yilmaz-kaan/OpenPhasedArray/Software/TXBoardData2/amp_imbalance.png

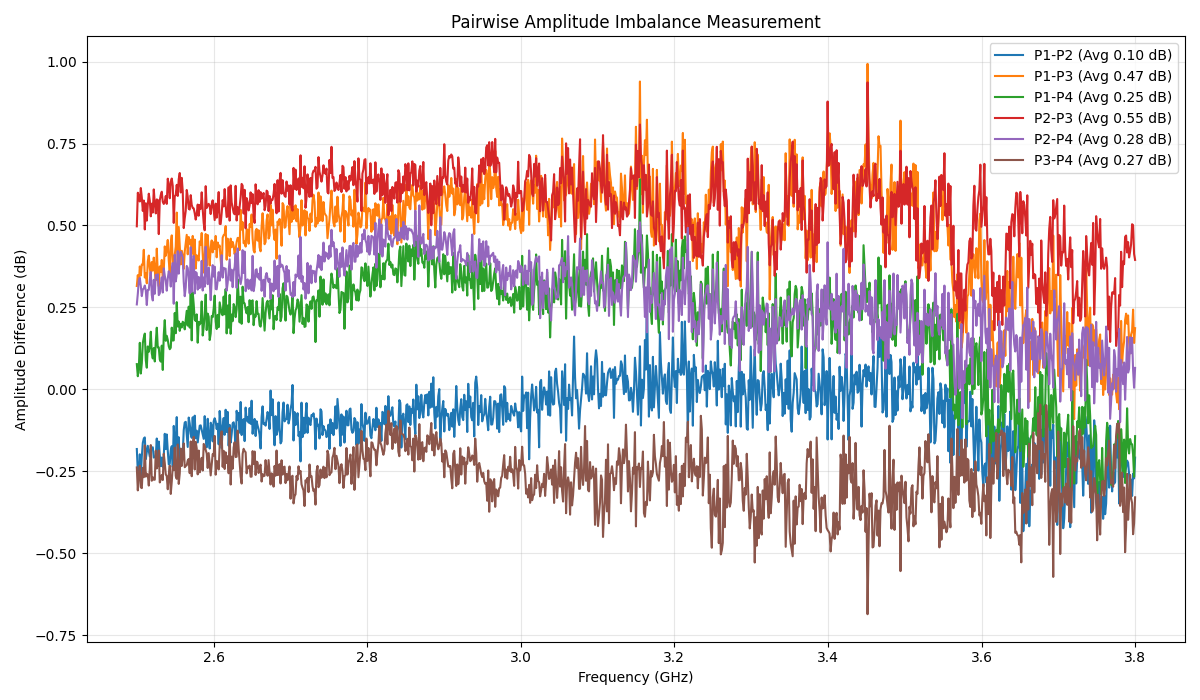
Software/TXBoardData2/amp_imbalance.png
