yilmaz-kaan/OpenPhasedArray/Software/TXBoardData2/phase_imbalance.png

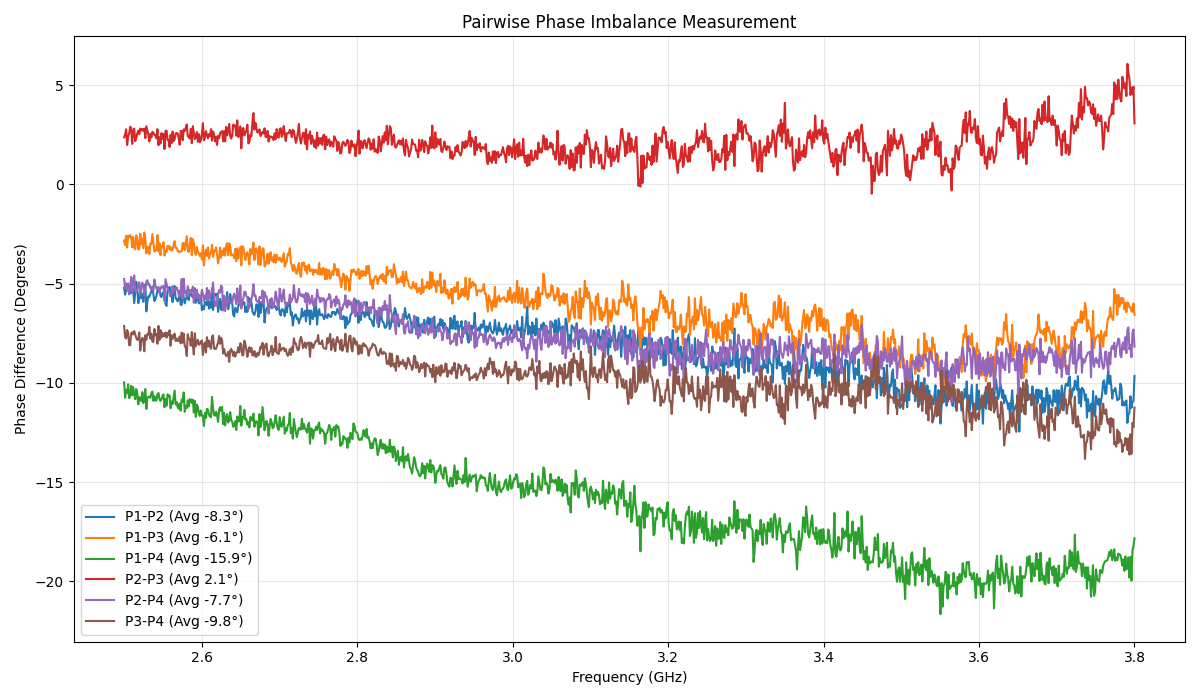
Software/TXBoardData2/phase_imbalance.png
