yilmaz-kaan/OpenPhasedArray/Software/TXBoardData2/s21_magnitude_plot.png

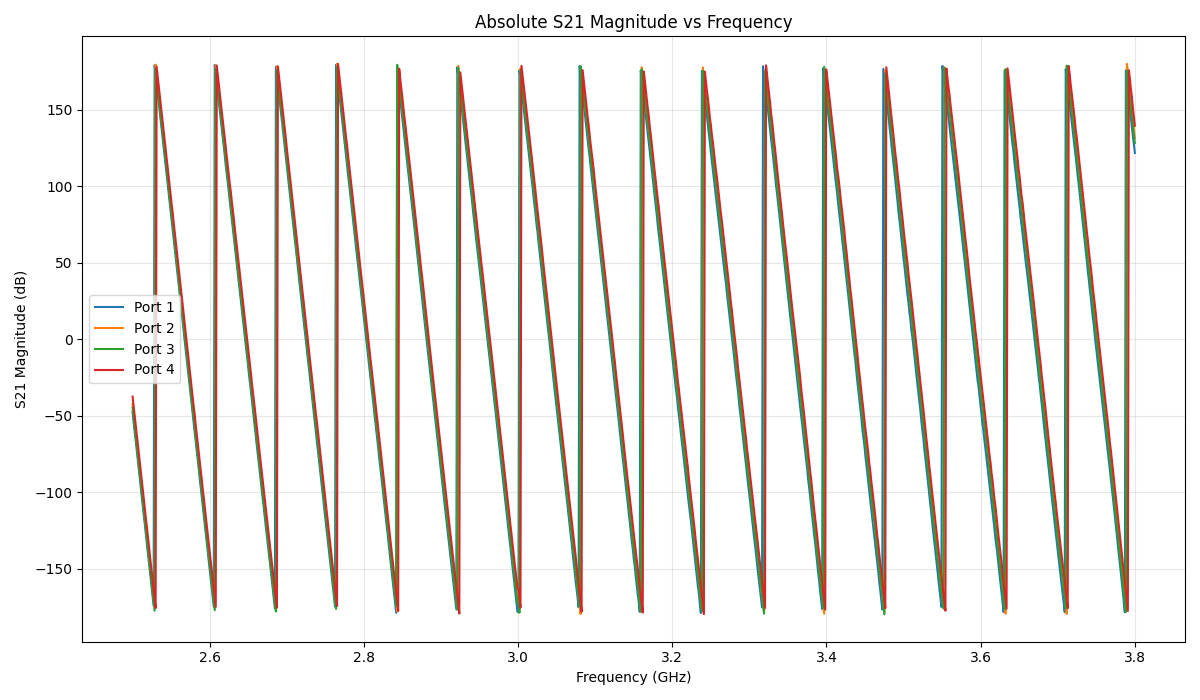
Software/TXBoardData2/s21_magnitude_plot.png
