yilmaz-kaan/OpenPhasedArray/Software/ChamberTesting/sweep_results/ang_+000/phase_sweep_20260409_190627.csv

timestamp | n | m | ph1 | ph2 | ph3 | ph4 | power_dbm | freq_hz
2026-04-09T19:06:29.300982 | 0 | 0 | 0 | 0 | 0 | 0 | -71.4100 | 2399999999.90
2026-04-09T19:06:31.392526 | 0 | 1 | 0 | 1 | 2 | 3 | -72.4100 | 2399999999.90
2026-04-09T19:06:33.485229 | 0 | 2 | 0 | 2 | 4 | 6 | -72.1000 | 2399999999.80
2026-04-09T19:06:35.580663 | 0 | 3 | 0 | 3 | 6 | 9 | -71.8600 | 2399999999.90
2026-04-09T19:06:37.671744 | 0 | 4 | 0 | 4 | 8 | 12 | -71.1500 | 2399999999.69
2026-04-09T19:06:39.762542 | 0 | 5 | 0 | 5 | 10 | 15 | -70.4400 | 2399999999.90
2026-04-09T19:06:41.852031 | 0 | 6 | 0 | 6 | 12 | 18 | -69.8200 | 2399999999.90
2026-04-09T19:06:43.941766 | 0 | 7 | 0 | 7 | 14 | 21 | -69.1300 | 2399999999.90
2026-04-09T19:06:46.022581 | 0 | 8 | 0 | 8 | 16 | 24 | -68.7100 | 2399999999.90
2026-04-09T19:06:48.113687 | 0 | 9 | 0 | 9 | 18 | 27 | -68.4400 | 2399999999.90
2026-04-09T19:06:50.193851 | 0 | 10 | 0 | 10 | 20 | 30 | -68.3600 | 2399999999.90
2026-04-09T19:06:52.286126 | 0 | 11 | 0 | 11 | 22 | 33 | -68.3400 | 2400000000.00
2026-04-09T19:06:54.379145 | 0 | 12 | 0 | 12 | 24 | 36 | -68.5800 | 2399999999.90
2026-04-09T19:06:56.465394 | 0 | 13 | 0 | 13 | 26 | 39 | -68.9800 | 2400000000.00
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
