yilmaz-kaan/OpenPhasedArray/Software/ChamberTesting/sweep_results/ang_+010/phase_sweep_20260409_192429.csv

timestamp | n | m | ph1 | ph2 | ph3 | ph4 | power_dbm | freq_hz
2026-04-09T19:24:32.037245 | 0 | 0 | 0 | 0 | 0 | 0 | -70.7900 | 2399999999.90
2026-04-09T19:24:34.134366 | 0 | 1 | 0 | 1 | 2 | 3 | -70.7300 | 2400000000.00
2026-04-09T19:24:36.229806 | 0 | 2 | 0 | 2 | 4 | 6 | -70.2400 | 2399999999.80
2026-04-09T19:24:38.324632 | 0 | 3 | 0 | 3 | 6 | 9 | -69.7700 | 2399999999.90
2026-04-09T19:24:40.418706 | 0 | 4 | 0 | 4 | 8 | 12 | -69.6800 | 2400000000.00
2026-04-09T19:24:42.508899 | 0 | 5 | 0 | 5 | 10 | 15 | -69.3500 | 2400000000.00
2026-04-09T19:24:44.606124 | 0 | 6 | 0 | 6 | 12 | 18 | -69.2600 | 2399999999.90
2026-04-09T19:24:46.698053 | 0 | 7 | 0 | 7 | 14 | 21 | -69.0800 | 2400000000.00
2026-04-09T19:24:48.781957 | 0 | 8 | 0 | 8 | 16 | 24 | -69.2700 | 2400000000.00
2026-04-09T19:24:50.884232 | 0 | 9 | 0 | 9 | 18 | 27 | -69.4100 | 2399999999.90
2026-04-09T19:24:52.974033 | 0 | 10 | 0 | 10 | 20 | 30 | -69.7900 | 2399999999.80
2026-04-09T19:24:55.054822 | 0 | 11 | 0 | 11 | 22 | 33 | -69.9200 | 2399999999.90
2026-04-09T19:24:57.141785 | 0 | 12 | 0 | 12 | 24 | 36 | -70.3000 | 2400000000.00
2026-04-09T19:24:59.232864 | 0 | 13 | 0 | 13 | 26 | 39 | -70.1900 | 2399999999.90
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
