yilmaz-kaan/OpenPhasedArray/Software/ChamberTesting/sweep_results/ang_+015/phase_sweep_20260409_193331.csv

timestamp | n | m | ph1 | ph2 | ph3 | ph4 | power_dbm | freq_hz
2026-04-09T19:33:33.427099 | 0 | 0 | 0 | 0 | 0 | 0 | -71.9300 | 2399999999.90
2026-04-09T19:33:35.512890 | 0 | 1 | 0 | 1 | 2 | 3 | -70.1900 | 2399999999.80
2026-04-09T19:33:37.604410 | 0 | 2 | 0 | 2 | 4 | 6 | -69.3100 | 2399999999.90
2026-04-09T19:33:39.693443 | 0 | 3 | 0 | 3 | 6 | 9 | -68.3500 | 2400000000.00
2026-04-09T19:33:41.779738 | 0 | 4 | 0 | 4 | 8 | 12 | -68.2300 | 2399999999.90
2026-04-09T19:33:43.872867 | 0 | 5 | 0 | 5 | 10 | 15 | -67.8000 | 2400000000.00
2026-04-09T19:33:45.961199 | 0 | 6 | 0 | 6 | 12 | 18 | -67.7100 | 2400000000.00
2026-04-09T19:33:48.042742 | 0 | 7 | 0 | 7 | 14 | 21 | -67.5100 | 2399999999.80
2026-04-09T19:33:50.132148 | 0 | 8 | 0 | 8 | 16 | 24 | -67.6300 | 2399999999.90
2026-04-09T19:33:52.229259 | 0 | 9 | 0 | 9 | 18 | 27 | -67.6000 | 2399999999.90
2026-04-09T19:33:54.323774 | 0 | 10 | 0 | 10 | 20 | 30 | -67.6900 | 2399999999.90
2026-04-09T19:33:56.415985 | 0 | 11 | 0 | 11 | 22 | 33 | -67.5000 | 2399999999.90
2026-04-09T19:33:58.516901 | 0 | 12 | 0 | 12 | 24 | 36 | -67.5100 | 2400000000.00
2026-04-09T19:34:00.602896 | 0 | 13 | 0 | 13 | 26 | 39 | -67.1100 | 2399999999.90
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
