yilmaz-kaan/OpenPhasedArray/Software/ChamberTesting/sweep_results/ang_+020/phase_sweep_20260409_194232.csv

timestamp | n | m | ph1 | ph2 | ph3 | ph4 | power_dbm | freq_hz
2026-04-09T19:42:34.784234 | 0 | 0 | 0 | 0 | 0 | 0 | -66.1600 | 2400000000.00
2026-04-09T19:42:36.875792 | 0 | 1 | 0 | 1 | 2 | 3 | -65.5500 | 2399999999.90
2026-04-09T19:42:38.965969 | 0 | 2 | 0 | 2 | 4 | 6 | -65.2800 | 2399999999.90
2026-04-09T19:42:41.057895 | 0 | 3 | 0 | 3 | 6 | 9 | -64.9800 | 2399999999.90
2026-04-09T19:42:43.145978 | 0 | 4 | 0 | 4 | 8 | 12 | -64.9700 | 2399999999.90
2026-04-09T19:42:45.240022 | 0 | 5 | 0 | 5 | 10 | 15 | -64.8600 | 2399999999.90
2026-04-09T19:42:47.333413 | 0 | 6 | 0 | 6 | 12 | 18 | -64.8800 | 2399999999.90
2026-04-09T19:42:49.427156 | 0 | 7 | 0 | 7 | 14 | 21 | -64.8200 | 2400000000.00
2026-04-09T19:42:51.518538 | 0 | 8 | 0 | 8 | 16 | 24 | -64.8400 | 2399999999.90
2026-04-09T19:42:53.616594 | 0 | 9 | 0 | 9 | 18 | 27 | -64.8400 | 2399999999.90
2026-04-09T19:42:55.706537 | 0 | 10 | 0 | 10 | 20 | 30 | -64.7700 | 2399999999.80
2026-04-09T19:42:57.793736 | 0 | 11 | 0 | 11 | 22 | 33 | -64.6100 | 2399999999.90
2026-04-09T19:42:59.885695 | 0 | 12 | 0 | 12 | 24 | 36 | -64.4500 | 2400000000.00
2026-04-09T19:43:01.974687 | 0 | 13 | 0 | 13 | 26 | 39 | -64.2200 | 2399999999.80
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
