yilmaz-kaan/OpenPhasedArray/Software/ChamberTesting/sweep_results/ang_+025/phase_sweep_20260409_195133.csv

timestamp | n | m | ph1 | ph2 | ph3 | ph4 | power_dbm | freq_hz
2026-04-09T19:51:35.974541 | 0 | 0 | 0 | 0 | 0 | 0 | -65.1900 | 2399999999.90
2026-04-09T19:51:38.059181 | 0 | 1 | 0 | 1 | 2 | 3 | -64.7200 | 2400000000.00
2026-04-09T19:51:40.144102 | 0 | 2 | 0 | 2 | 4 | 6 | -64.4900 | 2399999999.90
2026-04-09T19:51:42.229900 | 0 | 3 | 0 | 3 | 6 | 9 | -64.2400 | 2399999999.90
2026-04-09T19:51:44.320964 | 0 | 4 | 0 | 4 | 8 | 12 | -64.0500 | 2399999999.90
2026-04-09T19:51:46.420974 | 0 | 5 | 0 | 5 | 10 | 15 | -63.8100 | 2400000000.00
2026-04-09T19:51:48.504114 | 0 | 6 | 0 | 6 | 12 | 18 | -63.6700 | 2400000000.00
2026-04-09T19:51:50.597637 | 0 | 7 | 0 | 7 | 14 | 21 | -63.4800 | 2399999999.90
2026-04-09T19:51:52.689689 | 0 | 8 | 0 | 8 | 16 | 24 | -63.2700 | 2399999999.90
2026-04-09T19:51:54.782009 | 0 | 9 | 0 | 9 | 18 | 27 | -63.1600 | 2399999999.90
2026-04-09T19:51:56.870397 | 0 | 10 | 0 | 10 | 20 | 30 | -62.9600 | 2399999999.90
2026-04-09T19:51:58.956115 | 0 | 11 | 0 | 11 | 22 | 33 | -62.8100 | 2399999999.90
2026-04-09T19:52:01.042364 | 0 | 12 | 0 | 12 | 24 | 36 | -62.5600 | 2399999999.90
2026-04-09T19:52:03.135037 | 0 | 13 | 0 | 13 | 26 | 39 | -62.4800 | 2400000000.00
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
