yilmaz-kaan/OpenPhasedArray/Software/ChamberTesting/sweep_results/ang_+030/phase_sweep_20260409_200035.csv

timestamp | n | m | ph1 | ph2 | ph3 | ph4 | power_dbm | freq_hz
2026-04-09T20:00:37.349513 | 0 | 0 | 0 | 0 | 0 | 0 | -67.6800 | 2399999999.90
2026-04-09T20:00:39.437083 | 0 | 1 | 0 | 1 | 2 | 3 | -67.1000 | 2399999999.90
2026-04-09T20:00:41.528277 | 0 | 2 | 0 | 2 | 4 | 6 | -66.8000 | 2399999999.90
2026-04-09T20:00:43.612792 | 0 | 3 | 0 | 3 | 6 | 9 | -66.3300 | 2399999999.90
2026-04-09T20:00:45.705344 | 0 | 4 | 0 | 4 | 8 | 12 | -65.9500 | 2399999999.80
2026-04-09T20:00:47.785598 | 0 | 5 | 0 | 5 | 10 | 15 | -65.4100 | 2399999999.90
2026-04-09T20:00:49.880581 | 0 | 6 | 0 | 6 | 12 | 18 | -65.0500 | 2400000000.00
2026-04-09T20:00:51.974999 | 0 | 7 | 0 | 7 | 14 | 21 | -64.6100 | 2399999999.80
2026-04-09T20:00:54.067591 | 0 | 8 | 0 | 8 | 16 | 24 | -64.1400 | 2400000000.00
2026-04-09T20:00:56.161253 | 0 | 9 | 0 | 9 | 18 | 27 | -63.8400 | 2399999999.90
2026-04-09T20:00:58.252232 | 0 | 10 | 0 | 10 | 20 | 30 | -63.4700 | 2399999999.90
2026-04-09T20:01:00.339875 | 0 | 11 | 0 | 11 | 22 | 33 | -63.2100 | 2399999999.90
2026-04-09T20:01:02.432898 | 0 | 12 | 0 | 12 | 24 | 36 | -62.8500 | 2400000000.00
2026-04-09T20:01:04.521017 | 0 | 13 | 0 | 13 | 26 | 39 | -62.7200 | 2400000000.00
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
