yilmaz-kaan/OpenPhasedArray/Software/ChamberTesting/sweep_results/ang_-005/phase_sweep_20260409_185726.csv

timestamp | n | m | ph1 | ph2 | ph3 | ph4 | power_dbm | freq_hz
2026-04-09T18:57:28.192007 | 0 | 0 | 0 | 0 | 0 | 0 | -66.4600 | 2399999999.90
2026-04-09T18:57:30.276454 | 0 | 1 | 0 | 1 | 2 | 3 | -67.8800 | 2399999999.90
2026-04-09T18:57:32.355722 | 0 | 2 | 0 | 2 | 4 | 6 | -68.6300 | 2399999999.80
2026-04-09T18:57:34.439189 | 0 | 3 | 0 | 3 | 6 | 9 | -70.4000 | 2399999999.90
2026-04-09T18:57:36.528013 | 0 | 4 | 0 | 4 | 8 | 12 | -70.7800 | 2399999999.90
2026-04-09T18:57:38.619984 | 0 | 5 | 0 | 5 | 10 | 15 | -72.0100 | 2399999999.90
2026-04-09T18:57:40.705919 | 0 | 6 | 0 | 6 | 12 | 18 | -71.9600 | 2399999999.90
2026-04-09T18:57:42.796384 | 0 | 7 | 0 | 7 | 14 | 21 | -71.5200 | 2399999999.90
2026-04-09T18:57:44.882963 | 0 | 8 | 0 | 8 | 16 | 24 | -70.5100 | 2400000000.00
2026-04-09T18:57:46.976137 | 0 | 9 | 0 | 9 | 18 | 27 | -69.6900 | 2400000000.00
2026-04-09T18:57:49.063926 | 0 | 10 | 0 | 10 | 20 | 30 | -68.9200 | 2399999999.90
2026-04-09T18:57:51.150750 | 0 | 11 | 0 | 11 | 22 | 33 | -68.2800 | 2399999999.90
2026-04-09T18:57:53.241819 | 0 | 12 | 0 | 12 | 24 | 36 | -67.9100 | 2399999999.90
2026-04-09T18:57:55.326955 | 0 | 13 | 0 | 13 | 26 | 39 | -67.6500 | 2399999999.90
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
