yilmaz-kaan/OpenPhasedArray/Software/ChamberTesting/sweep_results/ang_-010/phase_sweep_20260409_184824.csv

timestamp | n | m | ph1 | ph2 | ph3 | ph4 | power_dbm | freq_hz
2026-04-09T18:48:26.828237 | 0 | 0 | 0 | 0 | 0 | 0 | -62.3600 | 2400000000.00
2026-04-09T18:48:28.917014 | 0 | 1 | 0 | 1 | 2 | 3 | -63.0900 | 2399999999.90
2026-04-09T18:48:31.004669 | 0 | 2 | 0 | 2 | 4 | 6 | -63.4000 | 2399999999.90
2026-04-09T18:48:33.090127 | 0 | 3 | 0 | 3 | 6 | 9 | -64.4400 | 2399999999.90
2026-04-09T18:48:35.181247 | 0 | 4 | 0 | 4 | 8 | 12 | -64.7000 | 2399999999.90
2026-04-09T18:48:37.275004 | 0 | 5 | 0 | 5 | 10 | 15 | -65.9300 | 2399999999.90
2026-04-09T18:48:39.377118 | 0 | 6 | 0 | 6 | 12 | 18 | -66.5300 | 2399999999.69
2026-04-09T18:48:41.471969 | 0 | 7 | 0 | 7 | 14 | 21 | -67.4100 | 2399999999.80
2026-04-09T18:48:43.563292 | 0 | 8 | 0 | 8 | 16 | 24 | -67.6000 | 2400000000.00
2026-04-09T18:48:45.664327 | 0 | 9 | 0 | 9 | 18 | 27 | -67.9100 | 2399999999.90
2026-04-09T18:48:47.746477 | 0 | 10 | 0 | 10 | 20 | 30 | -67.6400 | 2399999999.90
2026-04-09T18:48:49.832941 | 0 | 11 | 0 | 11 | 22 | 33 | -67.4000 | 2399999999.80
2026-04-09T18:48:51.922473 | 0 | 12 | 0 | 12 | 24 | 36 | -66.9500 | 2399999999.80
2026-04-09T18:48:54.012299 | 0 | 13 | 0 | 13 | 26 | 39 | -66.7200 | 2399999999.80
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
