yilmaz-kaan/OpenPhasedArray/Software/ChamberTesting/sweep_results/ang_-015/phase_sweep_20260409_183923.csv

timestamp | n | m | ph1 | ph2 | ph3 | ph4 | power_dbm | freq_hz
2026-04-09T18:39:25.411374 | 0 | 0 | 0 | 0 | 0 | 0 | -61.4100 | 2399999999.90
2026-04-09T18:39:27.498763 | 0 | 1 | 0 | 1 | 2 | 3 | -61.8200 | 2399999999.90
2026-04-09T18:39:29.592045 | 0 | 2 | 0 | 2 | 4 | 6 | -61.9200 | 2399999999.90
2026-04-09T18:39:31.675803 | 0 | 3 | 0 | 3 | 6 | 9 | -62.6400 | 2399999999.80
2026-04-09T18:39:33.763014 | 0 | 4 | 0 | 4 | 8 | 12 | -62.7400 | 2399999999.90
2026-04-09T18:39:35.848459 | 0 | 5 | 0 | 5 | 10 | 15 | -63.7600 | 2400000000.00
2026-04-09T18:39:37.932338 | 0 | 6 | 0 | 6 | 12 | 18 | -64.3100 | 2399999999.80
2026-04-09T18:39:40.013739 | 0 | 7 | 0 | 7 | 14 | 21 | -65.2500 | 2399999999.90
2026-04-09T18:39:42.097326 | 0 | 8 | 0 | 8 | 16 | 24 | -65.7100 | 2399999999.69
2026-04-09T18:39:44.189427 | 0 | 9 | 0 | 9 | 18 | 27 | -66.5000 | 2399999999.90
2026-04-09T18:39:46.275665 | 0 | 10 | 0 | 10 | 20 | 30 | -66.5600 | 2399999999.90
2026-04-09T18:39:48.365740 | 0 | 11 | 0 | 11 | 22 | 33 | -66.7300 | 2399999999.80
2026-04-09T18:39:50.452469 | 0 | 12 | 0 | 12 | 24 | 36 | -66.3000 | 2399999999.90
2026-04-09T18:39:52.536172 | 0 | 13 | 0 | 13 | 26 | 39 | -66.2000 | 2399999999.90
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
