yilmaz-kaan/OpenPhasedArray/Software/ChamberTesting/sweep_results/ang_-020/phase_sweep_20260409_183022.csv

timestamp | n | m | ph1 | ph2 | ph3 | ph4 | power_dbm | freq_hz
2026-04-09T18:30:24.312626 | 0 | 0 | 0 | 0 | 0 | 0 | -61.7200 | 2399999999.90
2026-04-09T18:30:26.401495 | 0 | 1 | 0 | 1 | 2 | 3 | -61.8700 | 2399999999.90
2026-04-09T18:30:28.493606 | 0 | 2 | 0 | 2 | 4 | 6 | -61.8400 | 2399999999.90
2026-04-09T18:30:30.581698 | 0 | 3 | 0 | 3 | 6 | 9 | -62.3400 | 2399999999.90
2026-04-09T18:30:32.667166 | 0 | 4 | 0 | 4 | 8 | 12 | -62.3700 | 2399999999.90
2026-04-09T18:30:34.753015 | 0 | 5 | 0 | 5 | 10 | 15 | -63.2900 | 2399999999.90
2026-04-09T18:30:36.840431 | 0 | 6 | 0 | 6 | 12 | 18 | -63.8500 | 2400000000.00
2026-04-09T18:30:38.930075 | 0 | 7 | 0 | 7 | 14 | 21 | -64.9200 | 2399999999.90
2026-04-09T18:30:41.011948 | 0 | 8 | 0 | 8 | 16 | 24 | -65.6900 | 2399999999.90
2026-04-09T18:30:43.105314 | 0 | 9 | 0 | 9 | 18 | 27 | -66.9700 | 2399999999.80
2026-04-09T18:30:45.199065 | 0 | 10 | 0 | 10 | 20 | 30 | -67.4600 | 2399999999.90
2026-04-09T18:30:47.291586 | 0 | 11 | 0 | 11 | 22 | 33 | -68.2000 | 2399999999.90
2026-04-09T18:30:49.380776 | 0 | 12 | 0 | 12 | 24 | 36 | -67.8000 | 2399999999.90
2026-04-09T18:30:51.468714 | 0 | 13 | 0 | 13 | 26 | 39 | -67.8200 | 2399999999.90
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
