yilmaz-kaan/OpenPhasedArray/Software/ChamberTesting/sweep_results/ang_-025/phase_sweep_20260409_182120.csv

timestamp | n | m | ph1 | ph2 | ph3 | ph4 | power_dbm | freq_hz
2026-04-09T18:21:23.060092 | 0 | 0 | 0 | 0 | 0 | 0 | -62.3700 | 2399999999.90
2026-04-09T18:21:25.151807 | 0 | 1 | 0 | 1 | 2 | 3 | -62.1000 | 2399999999.90
2026-04-09T18:21:27.238022 | 0 | 2 | 0 | 2 | 4 | 6 | -61.7800 | 2399999999.90
2026-04-09T18:21:29.328808 | 0 | 3 | 0 | 3 | 6 | 9 | -61.8900 | 2399999999.90
2026-04-09T18:21:31.416104 | 0 | 4 | 0 | 4 | 8 | 12 | -61.7000 | 2399999999.90
2026-04-09T18:21:33.501210 | 0 | 5 | 0 | 5 | 10 | 15 | -62.2500 | 2399999999.90
2026-04-09T18:21:35.586947 | 0 | 6 | 0 | 6 | 12 | 18 | -62.5900 | 2399999999.90
2026-04-09T18:21:37.673466 | 0 | 7 | 0 | 7 | 14 | 21 | -63.3500 | 2399999999.80
2026-04-09T18:21:39.764446 | 0 | 8 | 0 | 8 | 16 | 24 | -64.0500 | 2399999999.90
2026-04-09T18:21:41.854943 | 0 | 9 | 0 | 9 | 18 | 27 | -65.2900 | 2399999999.90
2026-04-09T18:21:43.938961 | 0 | 10 | 0 | 10 | 20 | 30 | -66.0900 | 2399999999.90
2026-04-09T18:21:46.026299 | 0 | 11 | 0 | 11 | 22 | 33 | -67.4700 | 2400000000.00
2026-04-09T18:21:48.117336 | 0 | 12 | 0 | 12 | 24 | 36 | -67.7700 | 2399999999.90
2026-04-09T18:21:50.204331 | 0 | 13 | 0 | 13 | 26 | 39 | -69.1300 | 2400000000.00
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
