yilmaz-kaan/OpenPhasedArray/Software/ChamberTesting/sweep_results/ang_-035/phase_sweep_20260409_180318.csv

timestamp | n | m | ph1 | ph2 | ph3 | ph4 | power_dbm | freq_hz
2026-04-09T18:03:20.436831 | 0 | 0 | 0 | 0 | 0 | 0 | -67.1000 | 2399999999.90
2026-04-09T18:03:22.525649 | 0 | 1 | 0 | 1 | 2 | 3 | -65.1200 | 2399999999.90
2026-04-09T18:03:24.610578 | 0 | 2 | 0 | 2 | 4 | 6 | -63.7500 | 2400000000.00
2026-04-09T18:03:26.697521 | 0 | 3 | 0 | 3 | 6 | 9 | -62.5800 | 2399999999.90
2026-04-09T18:03:28.790248 | 0 | 4 | 0 | 4 | 8 | 12 | -61.5300 | 2399999999.90
2026-04-09T18:03:30.880177 | 0 | 5 | 0 | 5 | 10 | 15 | -61.0200 | 2399999999.90
2026-04-09T18:03:32.971208 | 0 | 6 | 0 | 6 | 12 | 18 | -60.5900 | 2399999999.90
2026-04-09T18:03:35.060376 | 0 | 7 | 0 | 7 | 14 | 21 | -60.4100 | 2399999999.90
2026-04-09T18:03:37.150701 | 0 | 8 | 0 | 8 | 16 | 24 | -60.2300 | 2400000000.00
2026-04-09T18:03:39.240715 | 0 | 9 | 0 | 9 | 18 | 27 | -60.4400 | 2399999999.90
2026-04-09T18:03:41.328871 | 0 | 10 | 0 | 10 | 20 | 30 | -60.4500 | 2400000000.00
2026-04-09T18:03:43.419530 | 0 | 11 | 0 | 11 | 22 | 33 | -60.8700 | 2400000000.00
2026-04-09T18:03:45.513066 | 0 | 12 | 0 | 12 | 24 | 36 | -60.8800 | 2399999999.90
2026-04-09T18:03:47.605980 | 0 | 13 | 0 | 13 | 26 | 39 | -61.7100 | 2399999999.90
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
