yilmaz-kaan/OpenPhasedArray/Software/ChamberTesting/sweep_results/ang_-040/phase_sweep_20260409_175417.csv

timestamp | n | m | ph1 | ph2 | ph3 | ph4 | power_dbm | freq_hz
2026-04-09T17:54:19.151934 | 0 | 0 | 0 | 0 | 0 | 0 | -75.1100 | 2400000000.00
2026-04-09T17:54:21.243373 | 0 | 1 | 0 | 1 | 2 | 3 | -70.5600 | 2399999999.90
2026-04-09T17:54:23.327611 | 0 | 2 | 0 | 2 | 4 | 6 | -67.9600 | 2400000000.00
2026-04-09T17:54:25.414566 | 0 | 3 | 0 | 3 | 6 | 9 | -65.6200 | 2400000000.00
2026-04-09T17:54:27.502780 | 0 | 4 | 0 | 4 | 8 | 12 | -63.9200 | 2399999999.90
2026-04-09T17:54:29.589251 | 0 | 5 | 0 | 5 | 10 | 15 | -62.7800 | 2399999999.90
2026-04-09T17:54:31.684606 | 0 | 6 | 0 | 6 | 12 | 18 | -61.9500 | 2400000000.00
2026-04-09T17:54:33.771700 | 0 | 7 | 0 | 7 | 14 | 21 | -61.3600 | 2399999999.90
2026-04-09T17:54:35.856507 | 0 | 8 | 0 | 8 | 16 | 24 | -60.8600 | 2399999999.90
2026-04-09T17:54:37.953209 | 0 | 9 | 0 | 9 | 18 | 27 | -60.7200 | 2399999999.90
2026-04-09T17:54:40.037995 | 0 | 10 | 0 | 10 | 20 | 30 | -60.4700 | 2399999999.90
2026-04-09T17:54:42.128389 | 0 | 11 | 0 | 11 | 22 | 33 | -60.6000 | 2400000000.00
2026-04-09T17:54:44.217147 | 0 | 12 | 0 | 12 | 24 | 36 | -60.4300 | 2399999999.80
2026-04-09T17:54:46.309638 | 0 | 13 | 0 | 13 | 26 | 39 | -60.9500 | 2400000000.00
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
