yilmaz-kaan/OpenPhasedArray/Software/ChamberTesting/sweep_results/ang_-045/phase_sweep_20260409_174515.csv

timestamp | n | m | ph1 | ph2 | ph3 | ph4 | power_dbm | freq_hz
2026-04-09T17:45:17.784557 | 0 | 0 | 0 | 0 | 0 | 0 | -72.0000 | 2400000000.00
2026-04-09T17:45:19.870456 | 0 | 1 | 0 | 1 | 2 | 3 | -77.6500 | 2399999999.90
2026-04-09T17:45:21.955014 | 0 | 2 | 0 | 2 | 4 | 6 | -83.1400 | 2400000000.00
2026-04-09T17:45:24.036863 | 0 | 3 | 0 | 3 | 6 | 9 | -75.9000 | 2400000000.00
2026-04-09T17:45:26.125243 | 0 | 4 | 0 | 4 | 8 | 12 | -71.3400 | 2400000000.00
2026-04-09T17:45:28.225228 | 0 | 5 | 0 | 5 | 10 | 15 | -68.2800 | 2400000000.00
2026-04-09T17:45:30.316985 | 0 | 6 | 0 | 6 | 12 | 18 | -66.4400 | 2400000000.00
2026-04-09T17:45:32.401524 | 0 | 7 | 0 | 7 | 14 | 21 | -65.0100 | 2400000000.00
2026-04-09T17:45:34.487278 | 0 | 8 | 0 | 8 | 16 | 24 | -63.8500 | 2399999999.90
2026-04-09T17:45:36.577236 | 0 | 9 | 0 | 9 | 18 | 27 | -63.1600 | 2399999999.90
2026-04-09T17:45:38.667676 | 0 | 10 | 0 | 10 | 20 | 30 | -62.4800 | 2400000000.00
2026-04-09T17:45:40.756836 | 0 | 11 | 0 | 11 | 22 | 33 | -62.2000 | 2399999999.90
2026-04-09T17:45:42.842500 | 0 | 12 | 0 | 12 | 24 | 36 | -61.7300 | 2399999999.90
2026-04-09T17:45:44.933302 | 0 | 13 | 0 | 13 | 26 | 39 | -61.8200 | 2399999999.90
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
