yilmaz-kaan/OpenPhasedArray/Software/ChamberTesting/sweep_results/ang_-050/phase_sweep_20260409_173614.csv

timestamp | n | m | ph1 | ph2 | ph3 | ph4 | power_dbm | freq_hz
2026-04-09T17:36:16.323650 | 0 | 0 | 0 | 0 | 0 | 0 | -64.7300 | 2399999999.90
2026-04-09T17:36:18.417299 | 0 | 1 | 0 | 1 | 2 | 3 | -66.6700 | 2399999999.90
2026-04-09T17:36:20.511242 | 0 | 2 | 0 | 2 | 4 | 6 | -68.5800 | 2399999999.90
2026-04-09T17:36:22.593365 | 0 | 3 | 0 | 3 | 6 | 9 | -72.3300 | 2399999999.90
2026-04-09T17:36:24.680290 | 0 | 4 | 0 | 4 | 8 | 12 | -76.5200 | 2399999999.90
2026-04-09T17:36:26.767257 | 0 | 5 | 0 | 5 | 10 | 15 | -80.8900 | 2399999999.90
2026-04-09T17:36:28.856698 | 0 | 6 | 0 | 6 | 12 | 18 | -77.4300 | 2400000000.00
2026-04-09T17:36:30.940249 | 0 | 7 | 0 | 7 | 14 | 21 | -72.9700 | 2399999999.90
2026-04-09T17:36:33.025387 | 0 | 8 | 0 | 8 | 16 | 24 | -69.9000 | 2399999999.90
2026-04-09T17:36:35.120266 | 0 | 9 | 0 | 9 | 18 | 27 | -67.9400 | 2399999999.69
2026-04-09T17:36:37.215762 | 0 | 10 | 0 | 10 | 20 | 30 | -66.3700 | 2399999999.90
2026-04-09T17:36:39.303521 | 0 | 11 | 0 | 11 | 22 | 33 | -65.3800 | 2400000000.00
2026-04-09T17:36:41.390295 | 0 | 12 | 0 | 12 | 24 | 36 | -64.3900 | 2399999999.90
2026-04-09T17:36:43.482615 | 0 | 13 | 0 | 13 | 26 | 39 | -63.8800 | 2399999999.69
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
