yilmaz-kaan/OpenPhasedArray/Software/ChamberTesting/sweep_results/ang_-055/phase_sweep_20260409_172712.csv

timestamp | n | m | ph1 | ph2 | ph3 | ph4 | power_dbm | freq_hz
2026-04-09T17:27:14.909526 | 0 | 0 | 0 | 0 | 0 | 0 | -62.2100 | 2399999999.90
2026-04-09T17:27:17.001431 | 0 | 1 | 0 | 1 | 2 | 3 | -63.2700 | 2399999999.90
2026-04-09T17:27:19.100863 | 0 | 2 | 0 | 2 | 4 | 6 | -64.1600 | 2399999999.90
2026-04-09T17:27:21.190888 | 0 | 3 | 0 | 3 | 6 | 9 | -65.9200 | 2399999999.90
2026-04-09T17:27:23.278071 | 0 | 4 | 0 | 4 | 8 | 12 | -67.4300 | 2399999999.90
2026-04-09T17:27:25.364029 | 0 | 5 | 0 | 5 | 10 | 15 | -70.1300 | 2399999999.90
2026-04-09T17:27:27.453947 | 0 | 6 | 0 | 6 | 12 | 18 | -72.9700 | 2399999999.90
2026-04-09T17:27:29.541008 | 0 | 7 | 0 | 7 | 14 | 21 | -77.1400 | 2400000000.00
2026-04-09T17:27:31.630493 | 0 | 8 | 0 | 8 | 16 | 24 | -78.9700 | 2400000000.00
2026-04-09T17:27:33.729769 | 0 | 9 | 0 | 9 | 18 | 27 | -75.9600 | 2399999999.90
2026-04-09T17:27:35.829762 | 0 | 10 | 0 | 10 | 20 | 30 | -72.6700 | 2399999999.90
2026-04-09T17:27:37.913689 | 0 | 11 | 0 | 11 | 22 | 33 | -70.2900 | 2400000000.00
2026-04-09T17:27:39.995909 | 0 | 12 | 0 | 12 | 24 | 36 | -68.4200 | 2399999999.90
2026-04-09T17:27:42.081560 | 0 | 13 | 0 | 13 | 26 | 39 | -67.0300 | 2399999999.90
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
