yilmaz-kaan/OpenPhasedArray/Software/ChamberTesting/sweep_results/ang_-060/phase_sweep_20260409_171811.csv

timestamp | n | m | ph1 | ph2 | ph3 | ph4 | power_dbm | freq_hz
2026-04-09T17:18:13.489690 | 0 | 0 | 0 | 0 | 0 | 0 | -62.3200 | 2399999999.80
2026-04-09T17:18:15.578959 | 0 | 1 | 0 | 1 | 2 | 3 | -63.0200 | 2399999999.90
2026-04-09T17:18:17.669073 | 0 | 2 | 0 | 2 | 4 | 6 | -63.5500 | 2399999999.90
2026-04-09T17:18:19.759928 | 0 | 3 | 0 | 3 | 6 | 9 | -64.7200 | 2399999999.90
2026-04-09T17:18:21.855470 | 0 | 4 | 0 | 4 | 8 | 12 | -65.6400 | 2399999999.90
2026-04-09T17:18:23.945764 | 0 | 5 | 0 | 5 | 10 | 15 | -67.4500 | 2399999999.90
2026-04-09T17:18:26.031287 | 0 | 6 | 0 | 6 | 12 | 18 | -69.1600 | 2400000000.00
2026-04-09T17:18:28.120226 | 0 | 7 | 0 | 7 | 14 | 21 | -71.8300 | 2399999999.80
2026-04-09T17:18:30.213617 | 0 | 8 | 0 | 8 | 16 | 24 | -75.4400 | 2399999999.90
2026-04-09T17:18:32.309556 | 0 | 9 | 0 | 9 | 18 | 27 | -82.3700 | 2399999999.90
2026-04-09T17:18:34.401650 | 0 | 10 | 0 | 10 | 20 | 30 | -96.9700 | 2400000000.60
2026-04-09T17:18:36.489450 | 0 | 11 | 0 | 11 | 22 | 33 | -81.3300 | 2399999999.90
2026-04-09T17:18:38.576625 | 0 | 12 | 0 | 12 | 24 | 36 | -76.2000 | 2399999999.90
2026-04-09T17:18:40.668422 | 0 | 13 | 0 | 13 | 26 | 39 | -72.6700 | 2400000000.00
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
