yilmaz-kaan/OpenPhasedArray/Software/ChamberTesting/sweep_results/ang_-065/phase_sweep_20260409_170909.csv

timestamp | n | m | ph1 | ph2 | ph3 | ph4 | power_dbm | freq_hz
2026-04-09T17:09:12.079152 | 0 | 0 | 0 | 0 | 0 | 0 | -63.1600 | 2399999999.90
2026-04-09T17:09:14.185051 | 0 | 1 | 0 | 1 | 2 | 3 | -63.5400 | 2399999999.90
2026-04-09T17:09:16.271172 | 0 | 2 | 0 | 2 | 4 | 6 | -63.7100 | 2399999999.90
2026-04-09T17:09:18.354841 | 0 | 3 | 0 | 3 | 6 | 9 | -64.4100 | 2399999999.80
2026-04-09T17:09:20.437109 | 0 | 4 | 0 | 4 | 8 | 12 | -64.8200 | 2399999999.90
2026-04-09T17:09:22.522528 | 0 | 5 | 0 | 5 | 10 | 15 | -65.9200 | 2399999999.90
2026-04-09T17:09:24.612013 | 0 | 6 | 0 | 6 | 12 | 18 | -66.8100 | 2399999999.90
2026-04-09T17:09:26.696609 | 0 | 7 | 0 | 7 | 14 | 21 | -68.1300 | 2399999999.90
2026-04-09T17:09:28.780253 | 0 | 8 | 0 | 8 | 16 | 24 | -69.5700 | 2400000000.00
2026-04-09T17:09:30.893786 | 0 | 9 | 0 | 9 | 18 | 27 | -71.6000 | 2399999999.90
2026-04-09T17:09:32.980211 | 0 | 10 | 0 | 10 | 20 | 30 | -73.5000 | 2399999999.90
2026-04-09T17:09:35.072867 | 0 | 11 | 0 | 11 | 22 | 33 | -75.9600 | 2400000000.00
2026-04-09T17:09:37.161279 | 0 | 12 | 0 | 12 | 24 | 36 | -77.7300 | 2399999999.80
2026-04-09T17:09:39.251549 | 0 | 13 | 0 | 13 | 26 | 39 | -78.3500 | 2399999999.90
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
