yilmaz-kaan/OpenPhasedArray/Software/ChamberTesting/sweep_results/ang_-070/phase_sweep_20260409_170008.csv

timestamp | n | m | ph1 | ph2 | ph3 | ph4 | power_dbm | freq_hz
2026-04-09T17:00:10.706867 | 0 | 0 | 0 | 0 | 0 | 0 | -63.9200 | 2399999999.90
2026-04-09T17:00:12.794855 | 0 | 1 | 0 | 1 | 2 | 3 | -63.9300 | 2400000000.00
2026-04-09T17:00:14.875543 | 0 | 2 | 0 | 2 | 4 | 6 | -63.7200 | 2399999999.69
2026-04-09T17:00:16.963616 | 0 | 3 | 0 | 3 | 6 | 9 | -63.9300 | 2399999999.90
2026-04-09T17:00:19.051681 | 0 | 4 | 0 | 4 | 8 | 12 | -63.8900 | 2399999999.90
2026-04-09T17:00:21.135661 | 0 | 5 | 0 | 5 | 10 | 15 | -64.4000 | 2399999999.90
2026-04-09T17:00:23.230662 | 0 | 6 | 0 | 6 | 12 | 18 | -64.6900 | 2399999999.90
2026-04-09T17:00:25.317203 | 0 | 7 | 0 | 7 | 14 | 21 | -65.2800 | 2399999999.90
2026-04-09T17:00:27.411981 | 0 | 8 | 0 | 8 | 16 | 24 | -65.8000 | 2399999999.90
2026-04-09T17:00:29.509379 | 0 | 9 | 0 | 9 | 18 | 27 | -66.6900 | 2399999999.90
2026-04-09T17:00:31.598373 | 0 | 10 | 0 | 10 | 20 | 30 | -67.3700 | 2400000000.00
2026-04-09T17:00:33.684211 | 0 | 11 | 0 | 11 | 22 | 33 | -68.4000 | 2399999999.90
2026-04-09T17:00:35.778018 | 0 | 12 | 0 | 12 | 24 | 36 | -69.1200 | 2399999999.90
2026-04-09T17:00:37.868557 | 0 | 13 | 0 | 13 | 26 | 39 | -70.6500 | 2400000000.00
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
