yilmaz-kaan/OpenPhasedArray/Software/ChamberTesting/sweep_results/ang_-075/phase_sweep_20260409_165107.csv

timestamp | n | m | ph1 | ph2 | ph3 | ph4 | power_dbm | freq_hz
2026-04-09T16:51:09.448323 | 0 | 0 | 0 | 0 | 0 | 0 | -66.9500 | 2399999999.90
2026-04-09T16:51:11.539643 | 0 | 1 | 0 | 1 | 2 | 3 | -66.4800 | 2399999999.90
2026-04-09T16:51:13.633045 | 0 | 2 | 0 | 2 | 4 | 6 | -65.8300 | 2399999999.90
2026-04-09T16:51:15.723175 | 0 | 3 | 0 | 3 | 6 | 9 | -65.4900 | 2399999999.80
2026-04-09T16:51:17.808797 | 0 | 4 | 0 | 4 | 8 | 12 | -64.9800 | 2399999999.90
2026-04-09T16:51:19.897760 | 0 | 5 | 0 | 5 | 10 | 15 | -64.9500 | 2399999999.80
2026-04-09T16:51:21.983209 | 0 | 6 | 0 | 6 | 12 | 18 | -64.7900 | 2399999999.90
2026-04-09T16:51:24.074786 | 0 | 7 | 0 | 7 | 14 | 21 | -64.8400 | 2399999999.90
2026-04-09T16:51:26.165005 | 0 | 8 | 0 | 8 | 16 | 24 | -64.8400 | 2399999999.90
2026-04-09T16:51:28.260600 | 0 | 9 | 0 | 9 | 18 | 27 | -65.1700 | 2399999999.90
2026-04-09T16:51:30.347703 | 0 | 10 | 0 | 10 | 20 | 30 | -65.3200 | 2399999999.90
2026-04-09T16:51:32.431823 | 0 | 11 | 0 | 11 | 22 | 33 | -65.7800 | 2399999999.90
2026-04-09T16:51:34.518733 | 0 | 12 | 0 | 12 | 24 | 36 | -65.9800 | 2399999999.80
2026-04-09T16:51:36.606438 | 0 | 13 | 0 | 13 | 26 | 39 | -66.8500 | 2399999999.90
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
