yilmaz-kaan/OpenPhasedArray/Software/ChamberTesting/sweep_results/ang_-080/phase_sweep_20260409_164205.csv

timestamp | n | m | ph1 | ph2 | ph3 | ph4 | power_dbm | freq_hz
2026-04-09T16:42:08.068258 | 0 | 0 | 0 | 0 | 0 | 0 | -71.3500 | 2399999999.90
2026-04-09T16:42:10.153433 | 0 | 1 | 0 | 1 | 2 | 3 | -70.1200 | 2399999999.90
2026-04-09T16:42:12.239358 | 0 | 2 | 0 | 2 | 4 | 6 | -68.9800 | 2399999999.90
2026-04-09T16:42:14.334582 | 0 | 3 | 0 | 3 | 6 | 9 | -68.1200 | 2399999999.90
2026-04-09T16:42:16.426474 | 0 | 4 | 0 | 4 | 8 | 12 | -67.2200 | 2400000000.00
2026-04-09T16:42:18.521631 | 0 | 5 | 0 | 5 | 10 | 15 | -66.7900 | 2400000000.00
2026-04-09T16:42:20.615437 | 0 | 6 | 0 | 6 | 12 | 18 | -66.3700 | 2400000000.00
2026-04-09T16:42:22.702686 | 0 | 7 | 0 | 7 | 14 | 21 | -66.1400 | 2399999999.90
2026-04-09T16:42:24.791341 | 0 | 8 | 0 | 8 | 16 | 24 | -65.8700 | 2399999999.90
2026-04-09T16:42:26.884949 | 0 | 9 | 0 | 9 | 18 | 27 | -65.9700 | 2399999999.90
2026-04-09T16:42:28.978398 | 0 | 10 | 0 | 10 | 20 | 30 | -65.9100 | 2399999999.90
2026-04-09T16:42:31.068746 | 0 | 11 | 0 | 11 | 22 | 33 | -66.1600 | 2400000000.00
2026-04-09T16:42:33.164227 | 0 | 12 | 0 | 12 | 24 | 36 | -66.1600 | 2399999999.90
2026-04-09T16:42:35.255908 | 0 | 13 | 0 | 13 | 26 | 39 | -66.7600 | 2400000000.00
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
