yilmaz-kaan/OpenPhasedArray/Software/ChamberTesting/sweep_results/ang_-085/phase_sweep_20260409_163304.csv

timestamp | n | m | ph1 | ph2 | ph3 | ph4 | power_dbm | freq_hz
2026-04-09T16:33:06.679459 | 0 | 0 | 0 | 0 | 0 | 0 | -72.5600 | 2399999999.90
2026-04-09T16:33:08.765127 | 0 | 1 | 0 | 1 | 2 | 3 | -71.5700 | 2399999999.90
2026-04-09T16:33:10.850814 | 0 | 2 | 0 | 2 | 4 | 6 | -70.5300 | 2399999999.90
2026-04-09T16:33:12.938890 | 0 | 3 | 0 | 3 | 6 | 9 | -69.8300 | 2400000000.00
2026-04-09T16:33:15.029591 | 0 | 4 | 0 | 4 | 8 | 12 | -68.8900 | 2399999999.90
2026-04-09T16:33:17.110533 | 0 | 5 | 0 | 5 | 10 | 15 | -68.4800 | 2399999999.90
2026-04-09T16:33:19.196189 | 0 | 6 | 0 | 6 | 12 | 18 | -68.0200 | 2400000000.00
2026-04-09T16:33:21.283658 | 0 | 7 | 0 | 7 | 14 | 21 | -67.7800 | 2399999999.90
2026-04-09T16:33:23.370938 | 0 | 8 | 0 | 8 | 16 | 24 | -67.3800 | 2400000000.00
2026-04-09T16:33:25.471868 | 0 | 9 | 0 | 9 | 18 | 27 | -67.3800 | 2400000000.00
2026-04-09T16:33:27.557961 | 0 | 10 | 0 | 10 | 20 | 30 | -67.1900 | 2400000000.00
2026-04-09T16:33:29.644068 | 0 | 11 | 0 | 11 | 22 | 33 | -67.2800 | 2400000000.00
2026-04-09T16:33:31.728305 | 0 | 12 | 0 | 12 | 24 | 36 | -67.1100 | 2399999999.90
2026-04-09T16:33:33.823671 | 0 | 13 | 0 | 13 | 26 | 39 | -67.4700 | 2399999999.90
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
