yilmaz-kaan/OpenPhasedArray/Software/ChamberTesting/sweep_results/ang_+000/phase_sweep_20260407_183524.csv

timestamp | n | m | ph1 | ph2 | ph3 | ph4 | power_dbm | freq_hz
2026-04-07T18:35:25.254510 | 0 | 0 | 0 | 0 | 0 | 0 | -66.4100 | 2345000000.00
2026-04-07T18:35:26.338778 | 0 | 1 | 0 | 1 | 2 | 3 | -69.9000 | 2345000000.19
2026-04-07T18:35:27.419734 | 0 | 2 | 0 | 2 | 4 | 6 | -74.2900 | 2345000000.10
2026-04-07T18:35:28.504744 | 0 | 3 | 0 | 3 | 6 | 9 | -79.9600 | 2344999999.90
2026-04-07T18:35:29.589453 | 0 | 4 | 0 | 4 | 8 | 12 | -76.0300 | 2345000000.00
2026-04-07T18:35:30.674445 | 0 | 5 | 0 | 5 | 10 | 15 | -71.0600 | 2345000000.00
2026-04-07T18:35:31.761510 | 0 | 6 | 0 | 6 | 12 | 18 | -68.7300 | 2345000000.10
2026-04-07T18:35:32.850894 | 0 | 7 | 0 | 7 | 14 | 21 | -66.8000 | 2345000000.10
2026-04-07T18:35:33.944357 | 0 | 8 | 0 | 8 | 16 | 24 | -65.6700 | 2345000000.00
2026-04-07T18:35:35.028220 | 0 | 9 | 0 | 9 | 18 | 27 | -65.0100 | 2345000000.19
2026-04-07T18:35:36.117717 | 0 | 10 | 0 | 10 | 20 | 30 | -64.3800 | 2345000000.00
2026-04-07T18:35:37.204380 | 0 | 11 | 0 | 11 | 22 | 33 | -64.2200 | 2345000000.10
2026-04-07T18:35:38.294602 | 0 | 12 | 0 | 12 | 24 | 36 | -63.8800 | 2345000000.00
2026-04-07T18:35:39.381313 | 0 | 13 | 0 | 13 | 26 | 39 | -64.4000 | 2345000000.00
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
