yilmaz-kaan/OpenPhasedArray/Software/ChamberTesting/sweep_results/ang_+005/phase_sweep_20260407_184009.csv

timestamp | n | m | ph1 | ph2 | ph3 | ph4 | power_dbm | freq_hz
2026-04-07T18:40:10.472432 | 0 | 0 | 0 | 0 | 0 | 0 | -76.3400 | 2345000000.00
2026-04-07T18:40:11.564448 | 0 | 1 | 0 | 1 | 2 | 3 | -80.1500 | 2345000000.10
2026-04-07T18:40:12.646777 | 0 | 2 | 0 | 2 | 4 | 6 | -76.4000 | 2345000000.00
2026-04-07T18:40:13.733267 | 0 | 3 | 0 | 3 | 6 | 9 | -71.4900 | 2345000000.00
2026-04-07T18:40:14.823278 | 0 | 4 | 0 | 4 | 8 | 12 | -68.7700 | 2345000000.00
2026-04-07T18:40:15.907960 | 0 | 5 | 0 | 5 | 10 | 15 | -67.0200 | 2345000000.00
2026-04-07T18:40:16.993411 | 0 | 6 | 0 | 6 | 12 | 18 | -66.0400 | 2345000000.00
2026-04-07T18:40:18.086027 | 0 | 7 | 0 | 7 | 14 | 21 | -65.2700 | 2345000000.00
2026-04-07T18:40:19.172678 | 0 | 8 | 0 | 8 | 16 | 24 | -64.9600 | 2345000000.00
2026-04-07T18:40:20.267675 | 0 | 9 | 0 | 9 | 18 | 27 | -65.0800 | 2345000000.00
2026-04-07T18:40:21.357484 | 0 | 10 | 0 | 10 | 20 | 30 | -65.0200 | 2345000000.00
2026-04-07T18:40:22.455392 | 0 | 11 | 0 | 11 | 22 | 33 | -65.3800 | 2345000000.10
2026-04-07T18:40:23.541853 | 0 | 12 | 0 | 12 | 24 | 36 | -65.4900 | 2345000000.00
2026-04-07T18:40:24.629794 | 0 | 13 | 0 | 13 | 26 | 39 | -66.8500 | 2345000000.00
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
