yilmaz-kaan/OpenPhasedArray/Software/ChamberTesting/sweep_results/ang_+010/phase_sweep_20260407_184454.csv

timestamp | n | m | ph1 | ph2 | ph3 | ph4 | power_dbm | freq_hz
2026-04-07T18:44:55.508069 | 0 | 0 | 0 | 0 | 0 | 0 | -79.2500 | 2345000000.00
2026-04-07T18:44:56.594229 | 0 | 1 | 0 | 1 | 2 | 3 | -73.9500 | 2345000000.00
2026-04-07T18:44:57.683695 | 0 | 2 | 0 | 2 | 4 | 6 | -71.1400 | 2345000000.10
2026-04-07T18:44:58.772009 | 0 | 3 | 0 | 3 | 6 | 9 | -68.6900 | 2345000000.00
2026-04-07T18:44:59.853037 | 0 | 4 | 0 | 4 | 8 | 12 | -66.9800 | 2345000000.00
2026-04-07T18:45:00.939046 | 0 | 5 | 0 | 5 | 10 | 15 | -66.0700 | 2345000000.00
2026-04-07T18:45:02.022025 | 0 | 6 | 0 | 6 | 12 | 18 | -65.5600 | 2345000000.10
2026-04-07T18:45:03.110438 | 0 | 7 | 0 | 7 | 14 | 21 | -65.2400 | 2345000000.00
2026-04-07T18:45:04.200002 | 0 | 8 | 0 | 8 | 16 | 24 | -65.2800 | 2345000000.10
2026-04-07T18:45:05.300569 | 0 | 9 | 0 | 9 | 18 | 27 | -65.7300 | 2345000000.00
2026-04-07T18:45:06.387530 | 0 | 10 | 0 | 10 | 20 | 30 | -65.9400 | 2345000000.00
2026-04-07T18:45:07.475918 | 0 | 11 | 0 | 11 | 22 | 33 | -66.5300 | 2345000000.00
2026-04-07T18:45:08.568606 | 0 | 12 | 0 | 12 | 24 | 36 | -66.8000 | 2345000000.00
2026-04-07T18:45:09.672428 | 0 | 13 | 0 | 13 | 26 | 39 | -68.5800 | 2345000000.00
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
