yilmaz-kaan/OpenPhasedArray/Software/ChamberTesting/sweep_results/ang_+015/phase_sweep_20260407_184939.csv

timestamp | n | m | ph1 | ph2 | ph3 | ph4 | power_dbm | freq_hz
2026-04-07T18:49:40.561766 | 0 | 0 | 0 | 0 | 0 | 0 | -70.9500 | 2345000000.00
2026-04-07T18:49:41.652562 | 0 | 1 | 0 | 1 | 2 | 3 | -69.0600 | 2345000000.00
2026-04-07T18:49:42.735583 | 0 | 2 | 0 | 2 | 4 | 6 | -67.8600 | 2345000000.10
2026-04-07T18:49:43.817591 | 0 | 3 | 0 | 3 | 6 | 9 | -66.7600 | 2345000000.00
2026-04-07T18:49:44.903767 | 0 | 4 | 0 | 4 | 8 | 12 | -65.7700 | 2345000000.19
2026-04-07T18:49:45.989472 | 0 | 5 | 0 | 5 | 10 | 15 | -65.4800 | 2345000000.00
2026-04-07T18:49:47.078122 | 0 | 6 | 0 | 6 | 12 | 18 | -65.4200 | 2345000000.00
2026-04-07T18:49:48.168320 | 0 | 7 | 0 | 7 | 14 | 21 | -65.4800 | 2345000000.00
2026-04-07T18:49:49.254555 | 0 | 8 | 0 | 8 | 16 | 24 | -65.9000 | 2345000000.10
2026-04-07T18:49:50.348447 | 0 | 9 | 0 | 9 | 18 | 27 | -66.6600 | 2345000000.10
2026-04-07T18:49:51.435155 | 0 | 10 | 0 | 10 | 20 | 30 | -67.1400 | 2345000000.10
2026-04-07T18:49:52.519097 | 0 | 11 | 0 | 11 | 22 | 33 | -67.8100 | 2345000000.10
2026-04-07T18:49:53.608819 | 0 | 12 | 0 | 12 | 24 | 36 | -68.2700 | 2345000000.10
2026-04-07T18:49:54.691846 | 0 | 13 | 0 | 13 | 26 | 39 | -70.1100 | 2345000000.00
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
