yilmaz-kaan/OpenPhasedArray/Software/ChamberTesting/sweep_results/ang_+020/phase_sweep_20260407_185424.csv

timestamp | n | m | ph1 | ph2 | ph3 | ph4 | power_dbm | freq_hz
2026-04-07T18:54:25.478594 | 0 | 0 | 0 | 0 | 0 | 0 | -68.7100 | 2345000000.10
2026-04-07T18:54:26.564523 | 0 | 1 | 0 | 1 | 2 | 3 | -67.8500 | 2345000000.00
2026-04-07T18:54:27.654736 | 0 | 2 | 0 | 2 | 4 | 6 | -67.3000 | 2345000000.10
2026-04-07T18:54:28.747756 | 0 | 3 | 0 | 3 | 6 | 9 | -66.9400 | 2345000000.00
2026-04-07T18:54:29.835277 | 0 | 4 | 0 | 4 | 8 | 12 | -66.4500 | 2345000000.00
2026-04-07T18:54:30.927772 | 0 | 5 | 0 | 5 | 10 | 15 | -66.7200 | 2345000000.00
2026-04-07T18:54:32.014986 | 0 | 6 | 0 | 6 | 12 | 18 | -67.1200 | 2345000000.00
2026-04-07T18:54:33.105528 | 0 | 7 | 0 | 7 | 14 | 21 | -67.6400 | 2344999999.90
2026-04-07T18:54:34.193311 | 0 | 8 | 0 | 8 | 16 | 24 | -68.5700 | 2345000000.00
2026-04-07T18:54:35.299077 | 0 | 9 | 0 | 9 | 18 | 27 | -69.7600 | 2345000000.00
2026-04-07T18:54:36.382897 | 0 | 10 | 0 | 10 | 20 | 30 | -70.6000 | 2345000000.10
2026-04-07T18:54:37.466733 | 0 | 11 | 0 | 11 | 22 | 33 | -71.2500 | 2345000000.00
2026-04-07T18:54:38.554044 | 0 | 12 | 0 | 12 | 24 | 36 | -71.8800 | 2345000000.00
2026-04-07T18:54:39.639653 | 0 | 13 | 0 | 13 | 26 | 39 | -72.6900 | 2345000000.00
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
