yilmaz-kaan/OpenPhasedArray/Software/ChamberTesting/sweep_results/ang_+025/phase_sweep_20260407_185909.csv

timestamp | n | m | ph1 | ph2 | ph3 | ph4 | power_dbm | freq_hz
2026-04-07T18:59:10.204827 | 0 | 0 | 0 | 0 | 0 | 0 | -68.3000 | 2345000000.00
2026-04-07T18:59:11.300915 | 0 | 1 | 0 | 1 | 2 | 3 | -68.0200 | 2345000000.00
2026-04-07T18:59:12.389760 | 0 | 2 | 0 | 2 | 4 | 6 | -67.8700 | 2345000000.00
2026-04-07T18:59:13.476500 | 0 | 3 | 0 | 3 | 6 | 9 | -68.0100 | 2345000000.10
2026-04-07T18:59:14.567576 | 0 | 4 | 0 | 4 | 8 | 12 | -67.8000 | 2345000000.00
2026-04-07T18:59:15.655100 | 0 | 5 | 0 | 5 | 10 | 15 | -68.4800 | 2345000000.00
2026-04-07T18:59:16.744422 | 0 | 6 | 0 | 6 | 12 | 18 | -69.1900 | 2345000000.00
2026-04-07T18:59:17.832449 | 0 | 7 | 0 | 7 | 14 | 21 | -70.0700 | 2345000000.10
2026-04-07T18:59:18.923816 | 0 | 8 | 0 | 8 | 16 | 24 | -71.3300 | 2345000000.10
2026-04-07T18:59:20.014875 | 0 | 9 | 0 | 9 | 18 | 27 | -72.7000 | 2345000000.00
2026-04-07T18:59:21.105877 | 0 | 10 | 0 | 10 | 20 | 30 | -73.5300 | 2345000000.10
2026-04-07T18:59:22.191884 | 0 | 11 | 0 | 11 | 22 | 33 | -73.8300 | 2345000000.00
2026-04-07T18:59:23.279075 | 0 | 12 | 0 | 12 | 24 | 36 | -74.3100 | 2345000000.19
2026-04-07T18:59:24.368205 | 0 | 13 | 0 | 13 | 26 | 39 | -73.7200 | 2345000000.10
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
