yilmaz-kaan/OpenPhasedArray/Software/ChamberTesting/sweep_results/ang_+030/phase_sweep_20260407_190354.csv

timestamp | n | m | ph1 | ph2 | ph3 | ph4 | power_dbm | freq_hz
2026-04-07T19:03:55.429351 | 0 | 0 | 0 | 0 | 0 | 0 | -68.5600 | 2345000000.00
2026-04-07T19:03:56.516935 | 0 | 1 | 0 | 1 | 2 | 3 | -68.4200 | 2345000000.10
2026-04-07T19:03:57.604008 | 0 | 2 | 0 | 2 | 4 | 6 | -68.3700 | 2345000000.00
2026-04-07T19:03:58.694177 | 0 | 3 | 0 | 3 | 6 | 9 | -68.5300 | 2344999999.90
2026-04-07T19:03:59.783547 | 0 | 4 | 0 | 4 | 8 | 12 | -68.3700 | 2345000000.10
2026-04-07T19:04:00.864220 | 0 | 5 | 0 | 5 | 10 | 15 | -68.9600 | 2345000000.10
2026-04-07T19:04:01.953463 | 0 | 6 | 0 | 6 | 12 | 18 | -69.5300 | 2345000000.00
2026-04-07T19:04:03.045372 | 0 | 7 | 0 | 7 | 14 | 21 | -70.1500 | 2345000000.19
2026-04-07T19:04:04.132279 | 0 | 8 | 0 | 8 | 16 | 24 | -70.9800 | 2345000000.00
2026-04-07T19:04:05.227012 | 0 | 9 | 0 | 9 | 18 | 27 | -71.7100 | 2345000000.00
2026-04-07T19:04:06.317772 | 0 | 10 | 0 | 10 | 20 | 30 | -72.0500 | 2345000000.00
2026-04-07T19:04:07.411485 | 0 | 11 | 0 | 11 | 22 | 33 | -72.1600 | 2345000000.00
2026-04-07T19:04:08.504200 | 0 | 12 | 0 | 12 | 24 | 36 | -72.6000 | 2345000000.10
2026-04-07T19:04:09.589180 | 0 | 13 | 0 | 13 | 26 | 39 | -72.2800 | 2345000000.00
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
