yilmaz-kaan/OpenPhasedArray/Software/ChamberTesting/sweep_results/ang_-010/phase_sweep_20260407_182553.csv

timestamp | n | m | ph1 | ph2 | ph3 | ph4 | power_dbm | freq_hz
2026-04-07T18:25:54.886006 | 0 | 0 | 0 | 0 | 0 | 0 | -58.0800 | 2345000000.00
2026-04-07T18:25:55.972689 | 0 | 1 | 0 | 1 | 2 | 3 | -59.2900 | 2345000000.00
2026-04-07T18:25:57.062444 | 0 | 2 | 0 | 2 | 4 | 6 | -60.4300 | 2345000000.00
2026-04-07T18:25:58.163828 | 0 | 3 | 0 | 3 | 6 | 9 | -62.3200 | 2345000000.10
2026-04-07T18:25:59.249724 | 0 | 4 | 0 | 4 | 8 | 12 | -64.2700 | 2345000000.10
2026-04-07T18:26:00.335832 | 0 | 5 | 0 | 5 | 10 | 15 | -67.4600 | 2345000000.10
2026-04-07T18:26:01.424354 | 0 | 6 | 0 | 6 | 12 | 18 | -71.1500 | 2345000000.00
2026-04-07T18:26:02.526832 | 0 | 7 | 0 | 7 | 14 | 21 | -78.6300 | 2345000000.00
2026-04-07T18:26:03.629545 | 0 | 8 | 0 | 8 | 16 | 24 | -83.8200 | 2345000000.19
2026-04-07T18:26:04.723220 | 0 | 9 | 0 | 9 | 18 | 27 | -74.5300 | 2345000000.00
2026-04-07T18:26:05.811937 | 0 | 10 | 0 | 10 | 20 | 30 | -70.2500 | 2345000000.10
2026-04-07T18:26:06.899727 | 0 | 11 | 0 | 11 | 22 | 33 | -68.1500 | 2345000000.19
2026-04-07T18:26:07.992721 | 0 | 12 | 0 | 12 | 24 | 36 | -66.2200 | 2345000000.10
2026-04-07T18:26:09.080939 | 0 | 13 | 0 | 13 | 26 | 39 | -64.9000 | 2345000000.10
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
