yilmaz-kaan/OpenPhasedArray/Software/ChamberTesting/sweep_results/ang_-015/phase_sweep_20260407_182108.csv

timestamp | n | m | ph1 | ph2 | ph3 | ph4 | power_dbm | freq_hz
2026-04-07T18:21:09.651226 | 0 | 0 | 0 | 0 | 0 | 0 | -55.9500 | 2345000000.00
2026-04-07T18:21:10.737695 | 0 | 1 | 0 | 1 | 2 | 3 | -56.6700 | 2345000000.00
2026-04-07T18:21:11.825662 | 0 | 2 | 0 | 2 | 4 | 6 | -57.3400 | 2345000000.10
2026-04-07T18:21:12.918896 | 0 | 3 | 0 | 3 | 6 | 9 | -58.4600 | 2344999999.90
2026-04-07T18:21:14.004421 | 0 | 4 | 0 | 4 | 8 | 12 | -59.5400 | 2345000000.00
2026-04-07T18:21:15.092403 | 0 | 5 | 0 | 5 | 10 | 15 | -61.2500 | 2345000000.00
2026-04-07T18:21:16.186554 | 0 | 6 | 0 | 6 | 12 | 18 | -62.9400 | 2345000000.10
2026-04-07T18:21:17.268453 | 0 | 7 | 0 | 7 | 14 | 21 | -65.4300 | 2345000000.10
2026-04-07T18:21:18.351759 | 0 | 8 | 0 | 8 | 16 | 24 | -68.7100 | 2345000000.00
2026-04-07T18:21:19.441918 | 0 | 9 | 0 | 9 | 18 | 27 | -74.1400 | 2345000000.00
2026-04-07T18:21:20.526213 | 0 | 10 | 0 | 10 | 20 | 30 | -83.9600 | 2344999999.80
2026-04-07T18:21:21.613991 | 0 | 11 | 0 | 11 | 22 | 33 | -81.0800 | 2345000000.00
2026-04-07T18:21:22.704424 | 0 | 12 | 0 | 12 | 24 | 36 | -73.5100 | 2345000000.10
2026-04-07T18:21:23.792823 | 0 | 13 | 0 | 13 | 26 | 39 | -69.1500 | 2345000000.00
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
