yilmaz-kaan/OpenPhasedArray/Software/ChamberTesting/sweep_results/ang_-020/phase_sweep_20260407_181623.csv

timestamp | n | m | ph1 | ph2 | ph3 | ph4 | power_dbm | freq_hz
2026-04-07T18:16:24.606582 | 0 | 0 | 0 | 0 | 0 | 0 | -54.9200 | 2345000000.10
2026-04-07T18:16:25.699804 | 0 | 1 | 0 | 1 | 2 | 3 | -55.2400 | 2345000000.10
2026-04-07T18:16:26.789541 | 0 | 2 | 0 | 2 | 4 | 6 | -55.5800 | 2345000000.00
2026-04-07T18:16:27.875323 | 0 | 3 | 0 | 3 | 6 | 9 | -56.1800 | 2345000000.00
2026-04-07T18:16:28.968207 | 0 | 4 | 0 | 4 | 8 | 12 | -56.7900 | 2345000000.00
2026-04-07T18:16:30.060246 | 0 | 5 | 0 | 5 | 10 | 15 | -57.8100 | 2345000000.10
2026-04-07T18:16:31.151048 | 0 | 6 | 0 | 6 | 12 | 18 | -58.7600 | 2345000000.00
2026-04-07T18:16:32.238145 | 0 | 7 | 0 | 7 | 14 | 21 | -60.1200 | 2345000000.00
2026-04-07T18:16:33.326998 | 0 | 8 | 0 | 8 | 16 | 24 | -61.7500 | 2345000000.00
2026-04-07T18:16:34.423537 | 0 | 9 | 0 | 9 | 18 | 27 | -64.0600 | 2345000000.00
2026-04-07T18:16:35.512313 | 0 | 10 | 0 | 10 | 20 | 30 | -66.5300 | 2345000000.19
2026-04-07T18:16:36.603247 | 0 | 11 | 0 | 11 | 22 | 33 | -69.7300 | 2345000000.00
2026-04-07T18:16:37.688257 | 0 | 12 | 0 | 12 | 24 | 36 | -75.2200 | 2345000000.10
2026-04-07T18:16:38.768633 | 0 | 13 | 0 | 13 | 26 | 39 | -89.1900 | 2345000000.19
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
