yilmaz-kaan/OpenPhasedArray/Software/ChamberTesting/sweep_results/ang_-025/phase_sweep_20260407_181138.csv

timestamp | n | m | ph1 | ph2 | ph3 | ph4 | power_dbm | freq_hz
2026-04-07T18:11:39.402675 | 0 | 0 | 0 | 0 | 0 | 0 | -54.8400 | 2345000000.00
2026-04-07T18:11:40.497421 | 0 | 1 | 0 | 1 | 2 | 3 | -54.8100 | 2345000000.00
2026-04-07T18:11:41.581918 | 0 | 2 | 0 | 2 | 4 | 6 | -54.8600 | 2345000000.10
2026-04-07T18:11:42.673220 | 0 | 3 | 0 | 3 | 6 | 9 | -55.0700 | 2345000000.00
2026-04-07T18:11:43.760731 | 0 | 4 | 0 | 4 | 8 | 12 | -55.3400 | 2345000000.00
2026-04-07T18:11:44.847048 | 0 | 5 | 0 | 5 | 10 | 15 | -55.9100 | 2345000000.00
2026-04-07T18:11:45.937504 | 0 | 6 | 0 | 6 | 12 | 18 | -56.4500 | 2345000000.00
2026-04-07T18:11:47.029792 | 0 | 7 | 0 | 7 | 14 | 21 | -57.2400 | 2345000000.10
2026-04-07T18:11:48.118708 | 0 | 8 | 0 | 8 | 16 | 24 | -58.2000 | 2345000000.10
2026-04-07T18:11:49.210188 | 0 | 9 | 0 | 9 | 18 | 27 | -59.5900 | 2345000000.00
2026-04-07T18:11:50.300415 | 0 | 10 | 0 | 10 | 20 | 30 | -60.8600 | 2345000000.10
2026-04-07T18:11:51.390343 | 0 | 11 | 0 | 11 | 22 | 33 | -62.4300 | 2345000000.00
2026-04-07T18:11:52.476448 | 0 | 12 | 0 | 12 | 24 | 36 | -64.4400 | 2345000000.00
2026-04-07T18:11:53.569918 | 0 | 13 | 0 | 13 | 26 | 39 | -68.1000 | 2345000000.10
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
