yilmaz-kaan/OpenPhasedArray/Software/ChamberTesting/sweep_results/ang_-030/phase_sweep_20260407_180653.csv

timestamp | n | m | ph1 | ph2 | ph3 | ph4 | power_dbm | freq_hz
2026-04-07T18:06:54.615536 | 0 | 0 | 0 | 0 | 0 | 0 | -55.5200 | 2345000000.00
2026-04-07T18:06:55.698899 | 0 | 1 | 0 | 1 | 2 | 3 | -55.1300 | 2345000000.00
2026-04-07T18:06:56.780116 | 0 | 2 | 0 | 2 | 4 | 6 | -54.9300 | 2345000000.00
2026-04-07T18:06:57.865542 | 0 | 3 | 0 | 3 | 6 | 9 | -54.7900 | 2345000000.10
2026-04-07T18:06:58.951033 | 0 | 4 | 0 | 4 | 8 | 12 | -54.7900 | 2345000000.00
2026-04-07T18:07:00.040053 | 0 | 5 | 0 | 5 | 10 | 15 | -55.0000 | 2345000000.00
2026-04-07T18:07:01.128717 | 0 | 6 | 0 | 6 | 12 | 18 | -55.2500 | 2345000000.10
2026-04-07T18:07:02.214803 | 0 | 7 | 0 | 7 | 14 | 21 | -55.6700 | 2345000000.10
2026-04-07T18:07:03.301182 | 0 | 8 | 0 | 8 | 16 | 24 | -56.2200 | 2345000000.00
2026-04-07T18:07:04.395729 | 0 | 9 | 0 | 9 | 18 | 27 | -57.1100 | 2345000000.00
2026-04-07T18:07:05.477496 | 0 | 10 | 0 | 10 | 20 | 30 | -57.8300 | 2345000000.00
2026-04-07T18:07:06.560575 | 0 | 11 | 0 | 11 | 22 | 33 | -58.8000 | 2345000000.00
2026-04-07T18:07:07.641955 | 0 | 12 | 0 | 12 | 24 | 36 | -59.9500 | 2345000000.10
2026-04-07T18:07:08.731050 | 0 | 13 | 0 | 13 | 26 | 39 | -61.9000 | 2345000000.10
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
