yilmaz-kaan/OpenPhasedArray/Software/ChamberTesting/sweep_results/ang_-035/phase_sweep_20260407_180208.csv

timestamp | n | m | ph1 | ph2 | ph3 | ph4 | power_dbm | freq_hz
2026-04-07T18:02:09.718719 | 0 | 0 | 0 | 0 | 0 | 0 | -57.0800 | 2345000000.00
2026-04-07T18:02:10.801962 | 0 | 1 | 0 | 1 | 2 | 3 | -56.3000 | 2345000000.10
2026-04-07T18:02:11.891793 | 0 | 2 | 0 | 2 | 4 | 6 | -55.8300 | 2345000000.10
2026-04-07T18:02:12.982644 | 0 | 3 | 0 | 3 | 6 | 9 | -55.3500 | 2345000000.00
2026-04-07T18:02:14.077214 | 0 | 4 | 0 | 4 | 8 | 12 | -55.0900 | 2345000000.10
2026-04-07T18:02:15.156375 | 0 | 5 | 0 | 5 | 10 | 15 | -54.9700 | 2345000000.00
2026-04-07T18:02:16.243073 | 0 | 6 | 0 | 6 | 12 | 18 | -54.9700 | 2345000000.10
2026-04-07T18:02:17.334139 | 0 | 7 | 0 | 7 | 14 | 21 | -55.0700 | 2345000000.19
2026-04-07T18:02:18.423999 | 0 | 8 | 0 | 8 | 16 | 24 | -55.3100 | 2345000000.10
2026-04-07T18:02:19.505957 | 0 | 9 | 0 | 9 | 18 | 27 | -55.8400 | 2345000000.00
2026-04-07T18:02:20.595904 | 0 | 10 | 0 | 10 | 20 | 30 | -56.2000 | 2345000000.00
2026-04-07T18:02:21.680873 | 0 | 11 | 0 | 11 | 22 | 33 | -56.8000 | 2345000000.00
2026-04-07T18:02:22.761982 | 0 | 12 | 0 | 12 | 24 | 36 | -57.4900 | 2345000000.00
2026-04-07T18:02:23.847992 | 0 | 13 | 0 | 13 | 26 | 39 | -58.7000 | 2345000000.00
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
