yilmaz-kaan/OpenPhasedArray/Software/ChamberTesting/sweep_results/ang_-040/phase_sweep_20260407_175723.csv

timestamp | n | m | ph1 | ph2 | ph3 | ph4 | power_dbm | freq_hz
2026-04-07T17:57:24.669869 | 0 | 0 | 0 | 0 | 0 | 0 | -59.9000 | 2345000000.00
2026-04-07T17:57:25.753733 | 0 | 1 | 0 | 1 | 2 | 3 | -58.5900 | 2345000000.10
2026-04-07T17:57:26.841478 | 0 | 2 | 0 | 2 | 4 | 6 | -57.7600 | 2344999999.90
2026-04-07T17:57:27.929322 | 0 | 3 | 0 | 3 | 6 | 9 | -56.8500 | 2345000000.00
2026-04-07T17:57:29.018669 | 0 | 4 | 0 | 4 | 8 | 12 | -56.2700 | 2345000000.00
2026-04-07T17:57:30.106292 | 0 | 5 | 0 | 5 | 10 | 15 | -55.7800 | 2345000000.19
2026-04-07T17:57:31.198563 | 0 | 6 | 0 | 6 | 12 | 18 | -55.4900 | 2345000000.10
2026-04-07T17:57:32.289878 | 0 | 7 | 0 | 7 | 14 | 21 | -55.2700 | 2344999999.90
2026-04-07T17:57:33.377176 | 0 | 8 | 0 | 8 | 16 | 24 | -55.1700 | 2345000000.00
2026-04-07T17:57:34.471075 | 0 | 9 | 0 | 9 | 18 | 27 | -55.3600 | 2345000000.00
2026-04-07T17:57:35.565712 | 0 | 10 | 0 | 10 | 20 | 30 | -55.4000 | 2345000000.00
2026-04-07T17:57:36.650149 | 0 | 11 | 0 | 11 | 22 | 33 | -55.7000 | 2345000000.00
2026-04-07T17:57:37.736943 | 0 | 12 | 0 | 12 | 24 | 36 | -56.0200 | 2345000000.10
2026-04-07T17:57:38.821519 | 0 | 13 | 0 | 13 | 26 | 39 | -56.6900 | 2345000000.10
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
