yilmaz-kaan/OpenPhasedArray/Software/ChamberTesting/sweep_results/ang_-045/phase_sweep_20260407_175238.csv

timestamp | n | m | ph1 | ph2 | ph3 | ph4 | power_dbm | freq_hz
2026-04-07T17:52:39.720013 | 0 | 0 | 0 | 0 | 0 | 0 | -65.0400 | 2345000000.10
2026-04-07T17:52:40.801440 | 0 | 1 | 0 | 1 | 2 | 3 | -62.6300 | 2345000000.10
2026-04-07T17:52:41.885754 | 0 | 2 | 0 | 2 | 4 | 6 | -61.0900 | 2344999999.90
2026-04-07T17:52:42.969331 | 0 | 3 | 0 | 3 | 6 | 9 | -59.4500 | 2345000000.00
2026-04-07T17:52:44.057602 | 0 | 4 | 0 | 4 | 8 | 12 | -58.3500 | 2345000000.00
2026-04-07T17:52:45.146854 | 0 | 5 | 0 | 5 | 10 | 15 | -57.3500 | 2345000000.00
2026-04-07T17:52:46.230837 | 0 | 6 | 0 | 6 | 12 | 18 | -56.6800 | 2345000000.00
2026-04-07T17:52:47.319773 | 0 | 7 | 0 | 7 | 14 | 21 | -56.0600 | 2345000000.10
2026-04-07T17:52:48.403316 | 0 | 8 | 0 | 8 | 16 | 24 | -55.5900 | 2345000000.00
2026-04-07T17:52:49.496063 | 0 | 9 | 0 | 9 | 18 | 27 | -55.4200 | 2345000000.19
2026-04-07T17:52:50.580022 | 0 | 10 | 0 | 10 | 20 | 30 | -55.1400 | 2345000000.00
2026-04-07T17:52:51.666501 | 0 | 11 | 0 | 11 | 22 | 33 | -55.1500 | 2345000000.00
2026-04-07T17:52:52.747824 | 0 | 12 | 0 | 12 | 24 | 36 | -55.1600 | 2344999999.90
2026-04-07T17:52:53.833179 | 0 | 13 | 0 | 13 | 26 | 39 | -55.4200 | 2344999999.90
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
