yilmaz-kaan/OpenPhasedArray/Software/ChamberTesting/sweep_results/ang_-050/phase_sweep_20260407_174753.csv

timestamp | n | m | ph1 | ph2 | ph3 | ph4 | power_dbm | freq_hz
2026-04-07T17:47:54.619295 | 0 | 0 | 0 | 0 | 0 | 0 | -72.0400 | 2345000000.00
2026-04-07T17:47:55.725942 | 0 | 1 | 0 | 1 | 2 | 3 | -68.4900 | 2345000000.00
2026-04-07T17:47:56.814406 | 0 | 2 | 0 | 2 | 4 | 6 | -65.7800 | 2345000000.10
2026-04-07T17:47:57.906937 | 0 | 3 | 0 | 3 | 6 | 9 | -63.1100 | 2345000000.10
2026-04-07T17:47:58.992802 | 0 | 4 | 0 | 4 | 8 | 12 | -61.2800 | 2345000000.00
2026-04-07T17:48:00.086604 | 0 | 5 | 0 | 5 | 10 | 15 | -59.7000 | 2345000000.10
2026-04-07T17:48:01.177250 | 0 | 6 | 0 | 6 | 12 | 18 | -58.6100 | 2345000000.10
2026-04-07T17:48:02.273666 | 0 | 7 | 0 | 7 | 14 | 21 | -57.6200 | 2345000000.10
2026-04-07T17:48:03.362356 | 0 | 8 | 0 | 8 | 16 | 24 | -56.7800 | 2345000000.00
2026-04-07T17:48:04.456200 | 0 | 9 | 0 | 9 | 18 | 27 | -56.3100 | 2345000000.00
2026-04-07T17:48:05.544512 | 0 | 10 | 0 | 10 | 20 | 30 | -55.7600 | 2345000000.00
2026-04-07T17:48:06.643317 | 0 | 11 | 0 | 11 | 22 | 33 | -55.5400 | 2345000000.00
2026-04-07T17:48:07.729132 | 0 | 12 | 0 | 12 | 24 | 36 | -55.2800 | 2344999999.90
2026-04-07T17:48:08.813244 | 0 | 13 | 0 | 13 | 26 | 39 | -55.2400 | 2345000000.10
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
