yilmaz-kaan/OpenPhasedArray/Software/ChamberTesting/sweep_results/ang_-055/phase_sweep_20260407_174308.csv

timestamp | n | m | ph1 | ph2 | ph3 | ph4 | power_dbm | freq_hz
2026-04-07T17:43:09.553940 | 0 | 0 | 0 | 0 | 0 | 0 | -69.7700 | 2345000000.00
2026-04-07T17:43:10.634215 | 0 | 1 | 0 | 1 | 2 | 3 | -72.5400 | 2345000000.10
2026-04-07T17:43:11.724593 | 0 | 2 | 0 | 2 | 4 | 6 | -71.9700 | 2345000000.10
2026-04-07T17:43:12.813118 | 0 | 3 | 0 | 3 | 6 | 9 | -69.1900 | 2345000000.00
2026-04-07T17:43:13.901885 | 0 | 4 | 0 | 4 | 8 | 12 | -66.2600 | 2345000000.00
2026-04-07T17:43:14.993639 | 0 | 5 | 0 | 5 | 10 | 15 | -63.7900 | 2344999999.90
2026-04-07T17:43:16.080964 | 0 | 6 | 0 | 6 | 12 | 18 | -62.0400 | 2345000000.10
2026-04-07T17:43:17.166322 | 0 | 7 | 0 | 7 | 14 | 21 | -60.5000 | 2345000000.00
2026-04-07T17:43:18.254187 | 0 | 8 | 0 | 8 | 16 | 24 | -59.1500 | 2345000000.00
2026-04-07T17:43:19.344337 | 0 | 9 | 0 | 9 | 18 | 27 | -58.2900 | 2345000000.19
2026-04-07T17:43:20.435894 | 0 | 10 | 0 | 10 | 20 | 30 | -57.3800 | 2345000000.00
2026-04-07T17:43:21.525361 | 0 | 11 | 0 | 11 | 22 | 33 | -56.9000 | 2345000000.10
2026-04-07T17:43:22.609675 | 0 | 12 | 0 | 12 | 24 | 36 | -56.3400 | 2345000000.00
2026-04-07T17:43:23.696653 | 0 | 13 | 0 | 13 | 26 | 39 | -55.9800 | 2345000000.00
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
