yilmaz-kaan/OpenPhasedArray/Software/ChamberTesting/sweep_results/ang_-060/phase_sweep_20260407_173823.csv

timestamp | n | m | ph1 | ph2 | ph3 | ph4 | power_dbm | freq_hz
2026-04-07T17:38:24.909662 | 0 | 0 | 0 | 0 | 0 | 0 | -66.5200 | 2345000000.10
2026-04-07T17:38:25.999198 | 0 | 1 | 0 | 1 | 2 | 3 | -68.8200 | 2345000000.00
2026-04-07T17:38:27.085229 | 0 | 2 | 0 | 2 | 4 | 6 | -70.8900 | 2345000000.10
2026-04-07T17:38:28.168007 | 0 | 3 | 0 | 3 | 6 | 9 | -73.5700 | 2345000000.00
2026-04-07T17:38:29.262177 | 0 | 4 | 0 | 4 | 8 | 12 | -72.6100 | 2345000000.00
2026-04-07T17:38:30.353208 | 0 | 5 | 0 | 5 | 10 | 15 | -69.4600 | 2345000000.00
2026-04-07T17:38:31.443315 | 0 | 6 | 0 | 6 | 12 | 18 | -66.5900 | 2345000000.10
2026-04-07T17:38:32.530594 | 0 | 7 | 0 | 7 | 14 | 21 | -64.2100 | 2345000000.10
2026-04-07T17:38:33.615477 | 0 | 8 | 0 | 8 | 16 | 24 | -62.1400 | 2345000000.00
2026-04-07T17:38:34.711532 | 0 | 9 | 0 | 9 | 18 | 27 | -60.7800 | 2345000000.00
2026-04-07T17:38:35.797911 | 0 | 10 | 0 | 10 | 20 | 30 | -59.4700 | 2345000000.00
2026-04-07T17:38:36.882713 | 0 | 11 | 0 | 11 | 22 | 33 | -58.7100 | 2345000000.10
2026-04-07T17:38:37.967103 | 0 | 12 | 0 | 12 | 24 | 36 | -57.8500 | 2345000000.10
2026-04-07T17:38:39.046894 | 0 | 13 | 0 | 13 | 26 | 39 | -57.1700 | 2345000000.00
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
