yilmaz-kaan/OpenPhasedArray/Software/ChamberTesting/sweep_results/ang_-065/phase_sweep_20260407_173338.csv

timestamp | n | m | ph1 | ph2 | ph3 | ph4 | power_dbm | freq_hz
2026-04-07T17:33:39.914852 | 0 | 0 | 0 | 0 | 0 | 0 | -67.0800 | 2345000000.00
2026-04-07T17:33:41.000505 | 0 | 1 | 0 | 1 | 2 | 3 | -68.5900 | 2345000000.10
2026-04-07T17:33:42.088047 | 0 | 2 | 0 | 2 | 4 | 6 | -69.9500 | 2345000000.19
2026-04-07T17:33:43.172960 | 0 | 3 | 0 | 3 | 6 | 9 | -71.7200 | 2345000000.00
2026-04-07T17:33:44.259379 | 0 | 4 | 0 | 4 | 8 | 12 | -72.5600 | 2345000000.10
2026-04-07T17:33:45.351725 | 0 | 5 | 0 | 5 | 10 | 15 | -71.2500 | 2345000000.00
2026-04-07T17:33:46.441969 | 0 | 6 | 0 | 6 | 12 | 18 | -68.7800 | 2345000000.00
2026-04-07T17:33:47.528650 | 0 | 7 | 0 | 7 | 14 | 21 | -66.5700 | 2345000000.00
2026-04-07T17:33:48.618381 | 0 | 8 | 0 | 8 | 16 | 24 | -64.3400 | 2345000000.00
2026-04-07T17:33:49.704409 | 0 | 9 | 0 | 9 | 18 | 27 | -62.9100 | 2345000000.00
2026-04-07T17:33:50.797357 | 0 | 10 | 0 | 10 | 20 | 30 | -61.4600 | 2345000000.10
2026-04-07T17:33:51.888994 | 0 | 11 | 0 | 11 | 22 | 33 | -60.6300 | 2345000000.10
2026-04-07T17:33:52.974226 | 0 | 12 | 0 | 12 | 24 | 36 | -59.6200 | 2345000000.10
2026-04-07T17:33:54.061428 | 0 | 13 | 0 | 13 | 26 | 39 | -58.8100 | 2345000000.10
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
