yilmaz-kaan/OpenPhasedArray/Software/ChamberTesting/sweep_results/ang_-070/phase_sweep_20260407_172853.csv

timestamp | n | m | ph1 | ph2 | ph3 | ph4 | power_dbm | freq_hz
2026-04-07T17:28:54.946145 | 0 | 0 | 0 | 0 | 0 | 0 | -66.3000 | 2345000000.10
2026-04-07T17:28:56.034610 | 0 | 1 | 0 | 1 | 2 | 3 | -66.5400 | 2345000000.00
2026-04-07T17:28:57.117528 | 0 | 2 | 0 | 2 | 4 | 6 | -66.7600 | 2345000000.00
2026-04-07T17:28:58.200384 | 0 | 3 | 0 | 3 | 6 | 9 | -67.0800 | 2345000000.00
2026-04-07T17:28:59.287895 | 0 | 4 | 0 | 4 | 8 | 12 | -67.6300 | 2345000000.00
2026-04-07T17:29:00.374057 | 0 | 5 | 0 | 5 | 10 | 15 | -67.9900 | 2345000000.00
2026-04-07T17:29:01.459883 | 0 | 6 | 0 | 6 | 12 | 18 | -67.6100 | 2345000000.10
2026-04-07T17:29:02.543821 | 0 | 7 | 0 | 7 | 14 | 21 | -67.2700 | 2345000000.00
2026-04-07T17:29:03.629473 | 0 | 8 | 0 | 8 | 16 | 24 | -66.1900 | 2345000000.00
2026-04-07T17:29:04.715158 | 0 | 9 | 0 | 9 | 18 | 27 | -65.4200 | 2345000000.10
2026-04-07T17:29:05.794360 | 0 | 10 | 0 | 10 | 20 | 30 | -64.2000 | 2345000000.10
2026-04-07T17:29:06.881955 | 0 | 11 | 0 | 11 | 22 | 33 | -63.5600 | 2345000000.00
2026-04-07T17:29:07.989619 | 0 | 12 | 0 | 12 | 24 | 36 | -62.4500 | 2345000000.00
2026-04-07T17:29:09.075845 | 0 | 13 | 0 | 13 | 26 | 39 | -61.5600 | 2345000000.00
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
