yilmaz-kaan/OpenPhasedArray/Software/ChamberTesting/sweep_results/ang_-075/phase_sweep_20260407_172408.csv

timestamp | n | m | ph1 | ph2 | ph3 | ph4 | power_dbm | freq_hz
2026-04-07T17:24:09.944722 | 0 | 0 | 0 | 0 | 0 | 0 | -65.8800 | 2345000000.10
2026-04-07T17:24:11.028369 | 0 | 1 | 0 | 1 | 2 | 3 | -65.5300 | 2345000000.00
2026-04-07T17:24:12.112283 | 0 | 2 | 0 | 2 | 4 | 6 | -65.4200 | 2345000000.10
2026-04-07T17:24:13.200441 | 0 | 3 | 0 | 3 | 6 | 9 | -65.3600 | 2345000000.00
2026-04-07T17:24:14.283654 | 0 | 4 | 0 | 4 | 8 | 12 | -65.8400 | 2345000000.00
2026-04-07T17:24:15.368362 | 0 | 5 | 0 | 5 | 10 | 15 | -66.2900 | 2344999999.90
2026-04-07T17:24:16.456341 | 0 | 6 | 0 | 6 | 12 | 18 | -66.5000 | 2345000000.00
2026-04-07T17:24:17.544608 | 0 | 7 | 0 | 7 | 14 | 21 | -67.0200 | 2345000000.00
2026-04-07T17:24:18.627930 | 0 | 8 | 0 | 8 | 16 | 24 | -67.1900 | 2345000000.10
2026-04-07T17:24:19.717726 | 0 | 9 | 0 | 9 | 18 | 27 | -67.4700 | 2345000000.10
2026-04-07T17:24:20.801401 | 0 | 10 | 0 | 10 | 20 | 30 | -66.9500 | 2345000000.19
2026-04-07T17:24:21.879735 | 0 | 11 | 0 | 11 | 22 | 33 | -66.8500 | 2345000000.00
2026-04-07T17:24:22.958544 | 0 | 12 | 0 | 12 | 24 | 36 | -65.8600 | 2345000000.10
2026-04-07T17:24:24.041565 | 0 | 13 | 0 | 13 | 26 | 39 | -64.8300 | 2345000000.00
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
