yilmaz-kaan/OpenPhasedArray/Software/ChamberTesting/sweep_results/ang_-080/phase_sweep_20260407_171924.csv

timestamp | n | m | ph1 | ph2 | ph3 | ph4 | power_dbm | freq_hz
2026-04-07T17:19:25.980054 | 0 | 0 | 0 | 0 | 0 | 0 | -66.7700 | 2345000000.00
2026-04-07T17:19:27.066506 | 0 | 1 | 0 | 1 | 2 | 3 | -66.2200 | 2345000000.10
2026-04-07T17:19:28.156424 | 0 | 2 | 0 | 2 | 4 | 6 | -65.9900 | 2345000000.00
2026-04-07T17:19:29.257523 | 0 | 3 | 0 | 3 | 6 | 9 | -65.7300 | 2344999999.90
2026-04-07T17:19:30.344161 | 0 | 4 | 0 | 4 | 8 | 12 | -66.1700 | 2345000000.19
2026-04-07T17:19:31.429479 | 0 | 5 | 0 | 5 | 10 | 15 | -66.4900 | 2345000000.10
2026-04-07T17:19:32.513326 | 0 | 6 | 0 | 6 | 12 | 18 | -66.7400 | 2345000000.00
2026-04-07T17:19:33.596962 | 0 | 7 | 0 | 7 | 14 | 21 | -67.3400 | 2345000000.00
2026-04-07T17:19:34.682246 | 0 | 8 | 0 | 8 | 16 | 24 | -67.8800 | 2345000000.00
2026-04-07T17:19:35.776865 | 0 | 9 | 0 | 9 | 18 | 27 | -68.6300 | 2345000000.00
2026-04-07T17:19:36.862772 | 0 | 10 | 0 | 10 | 20 | 30 | -68.7500 | 2345000000.00
2026-04-07T17:19:37.948531 | 0 | 11 | 0 | 11 | 22 | 33 | -69.2800 | 2345000000.00
2026-04-07T17:19:39.027798 | 0 | 12 | 0 | 12 | 24 | 36 | -68.7700 | 2345000000.00
2026-04-07T17:19:40.106336 | 0 | 13 | 0 | 13 | 26 | 39 | -67.8900 | 2345000000.00
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
