yilmaz-kaan/OpenPhasedArray/Software/ChamberTesting/sweep_results/ang_-085/phase_sweep_20260407_171440.csv

timestamp | n | m | ph1 | ph2 | ph3 | ph4 | power_dbm | freq_hz
2026-04-07T17:14:41.310542 | 0 | 0 | 0 | 0 | 0 | 0 | -69.4700 | 2345000000.10
2026-04-07T17:14:42.394565 | 0 | 1 | 0 | 1 | 2 | 3 | -68.9300 | 2345000000.00
2026-04-07T17:14:43.482296 | 0 | 2 | 0 | 2 | 4 | 6 | -68.6100 | 2345000000.10
2026-04-07T17:14:44.570803 | 0 | 3 | 0 | 3 | 6 | 9 | -68.2200 | 2345000000.10
2026-04-07T17:14:45.663125 | 0 | 4 | 0 | 4 | 8 | 12 | -68.5500 | 2345000000.10
2026-04-07T17:14:46.742005 | 0 | 5 | 0 | 5 | 10 | 15 | -68.6800 | 2345000000.00
2026-04-07T17:14:47.827440 | 0 | 6 | 0 | 6 | 12 | 18 | -68.7300 | 2345000000.00
2026-04-07T17:14:48.913180 | 0 | 7 | 0 | 7 | 14 | 21 | -69.0000 | 2345000000.00
2026-04-07T17:14:49.996336 | 0 | 8 | 0 | 8 | 16 | 24 | -69.2900 | 2345000000.10
2026-04-07T17:14:51.089344 | 0 | 9 | 0 | 9 | 18 | 27 | -69.7100 | 2345000000.00
2026-04-07T17:14:52.176396 | 0 | 10 | 0 | 10 | 20 | 30 | -69.6600 | 2345000000.00
2026-04-07T17:14:53.275333 | 0 | 11 | 0 | 11 | 22 | 33 | -70.0900 | 2345000000.00
2026-04-07T17:14:54.357847 | 0 | 12 | 0 | 12 | 24 | 36 | -69.7500 | 2345000000.00
2026-04-07T17:14:55.440994 | 0 | 13 | 0 | 13 | 26 | 39 | -69.1200 | 2345000000.00
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
