yilmaz-kaan/OpenPhasedArray/Software/ChamberTesting/extracted_patterns_polar/polar_steer_000deg.png

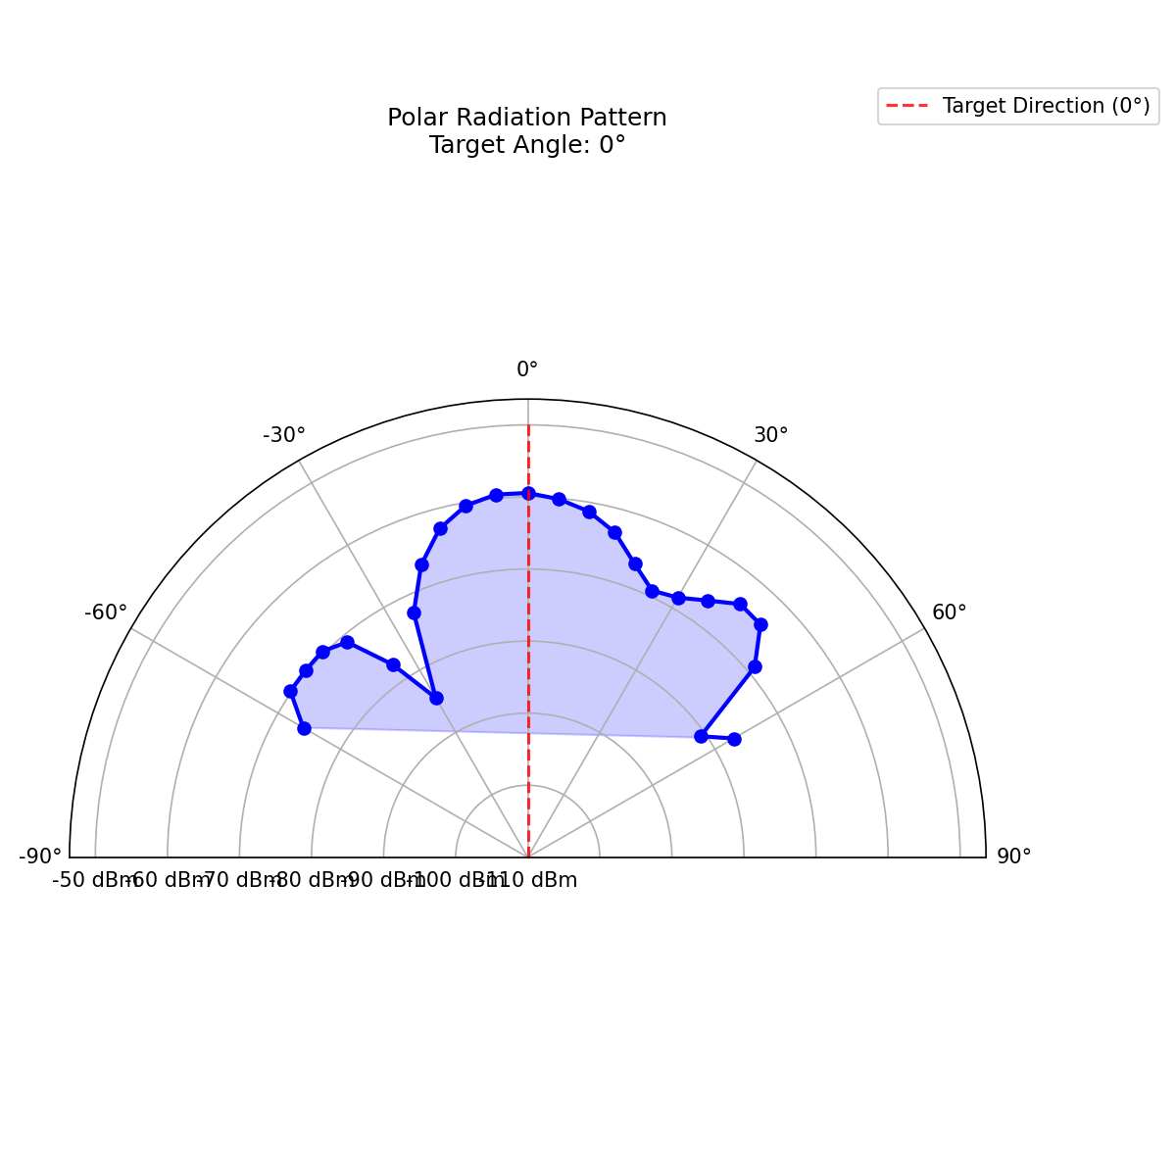
Software/ChamberTesting/extracted_patterns_polar/polar_steer_000deg.png
