yilmaz-kaan/OpenPhasedArray/Software/ChamberTesting/extracted_patterns_polar/polar_steer_010deg.png

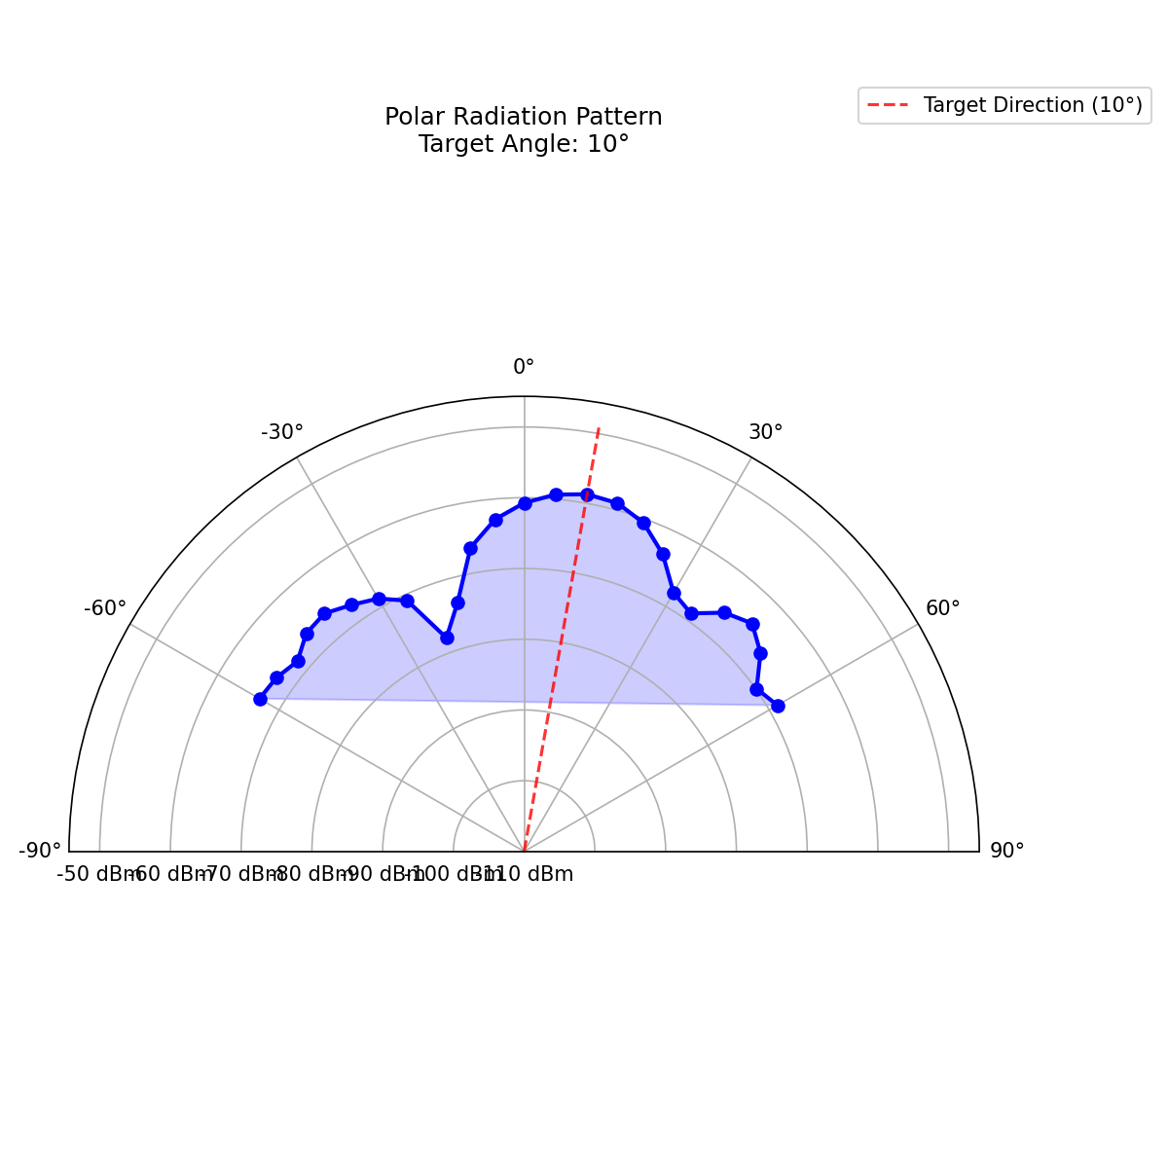
Software/ChamberTesting/extracted_patterns_polar/polar_steer_010deg.png
