yilmaz-kaan/OpenPhasedArray/Software/ChamberTesting/extracted_patterns_polar/polar_steer_040deg.png

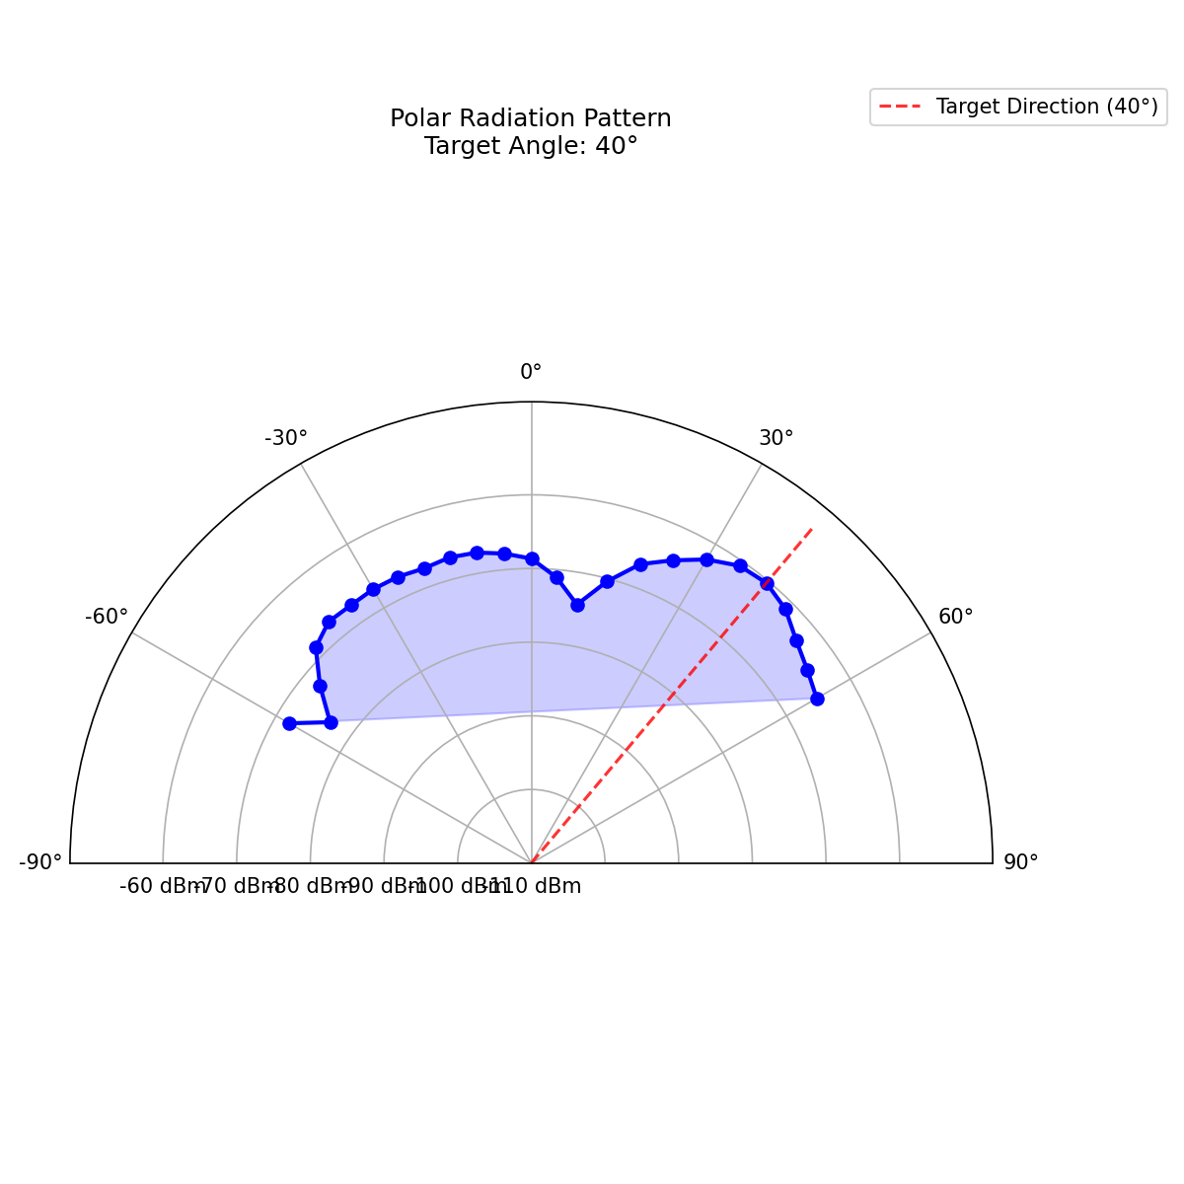
Software/ChamberTesting/extracted_patterns_polar/polar_steer_040deg.png
