yilmaz-kaan/OpenPhasedArray/Software/ChamberTesting/extracted_patterns_polar/polar_steer_055deg.png

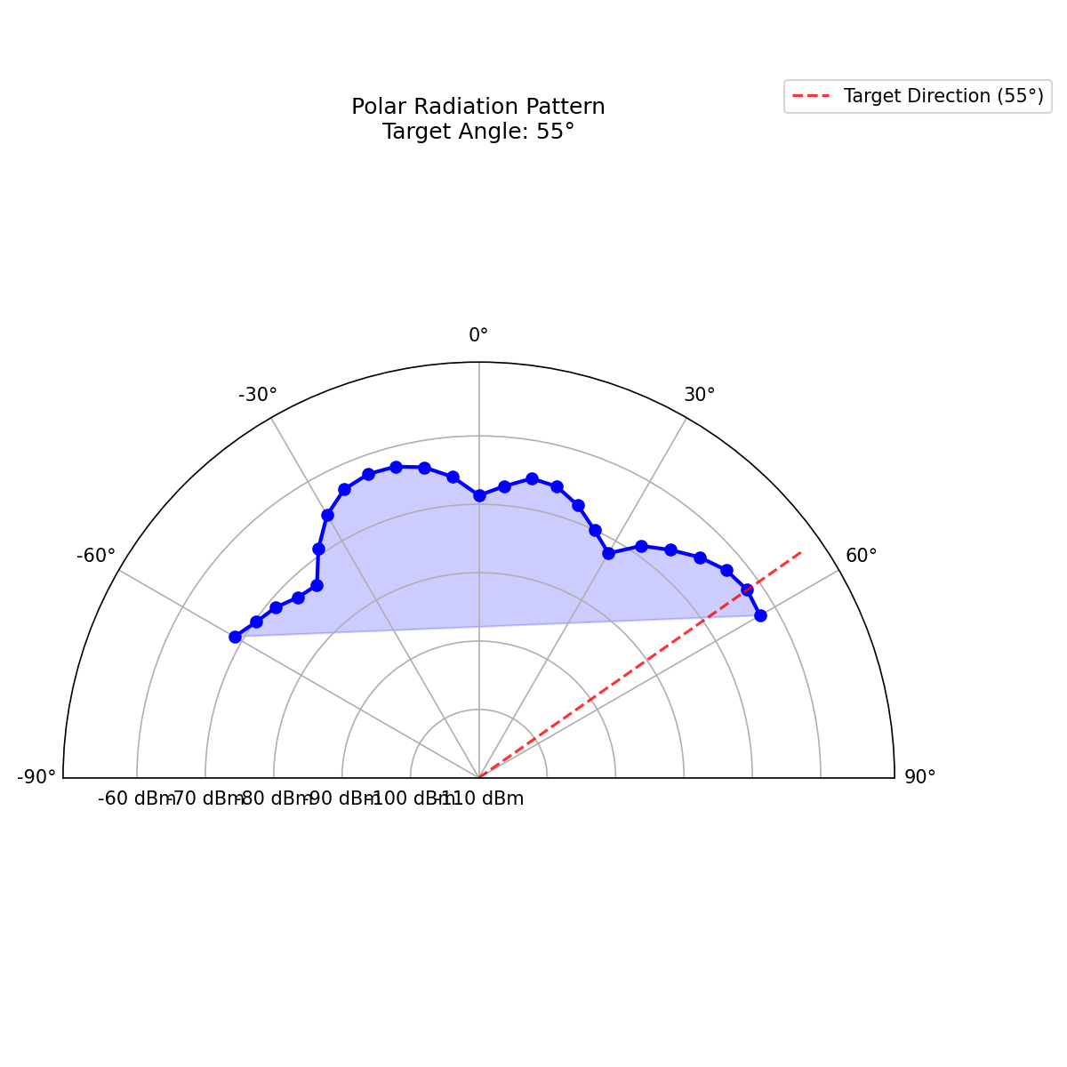
Software/ChamberTesting/extracted_patterns_polar/polar_steer_055deg.png
