yilmaz-kaan/OpenPhasedArray/Software/ChamberTesting/pattern_measurements/pattern_20260404_140905.png

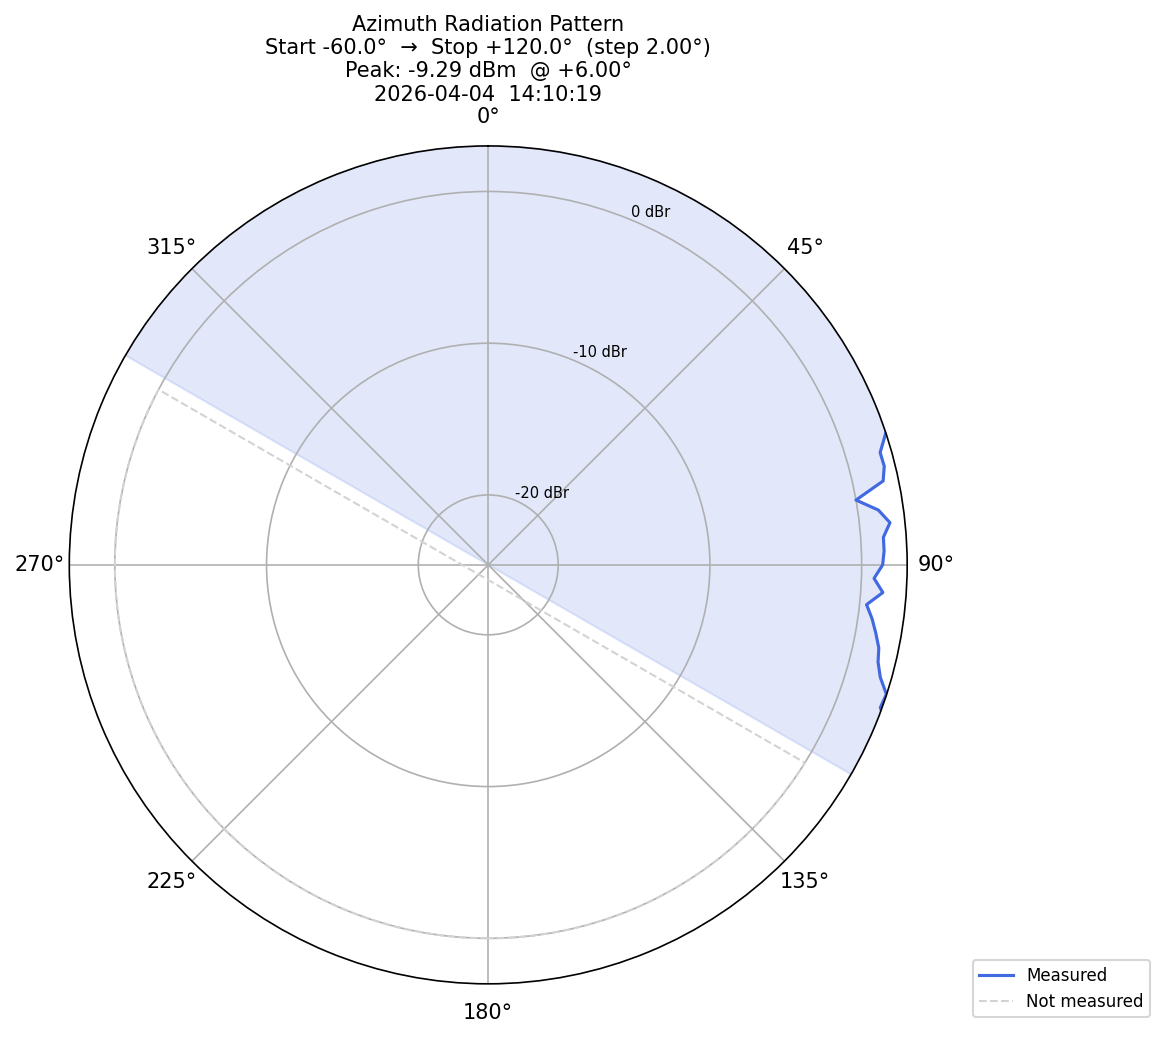
Software/ChamberTesting/pattern_measurements/pattern_20260404_140905.png
