yilmaz-kaan/OpenPhasedArray/Software/ChamberTesting/pattern_measurements/pattern_20260404_141123.png

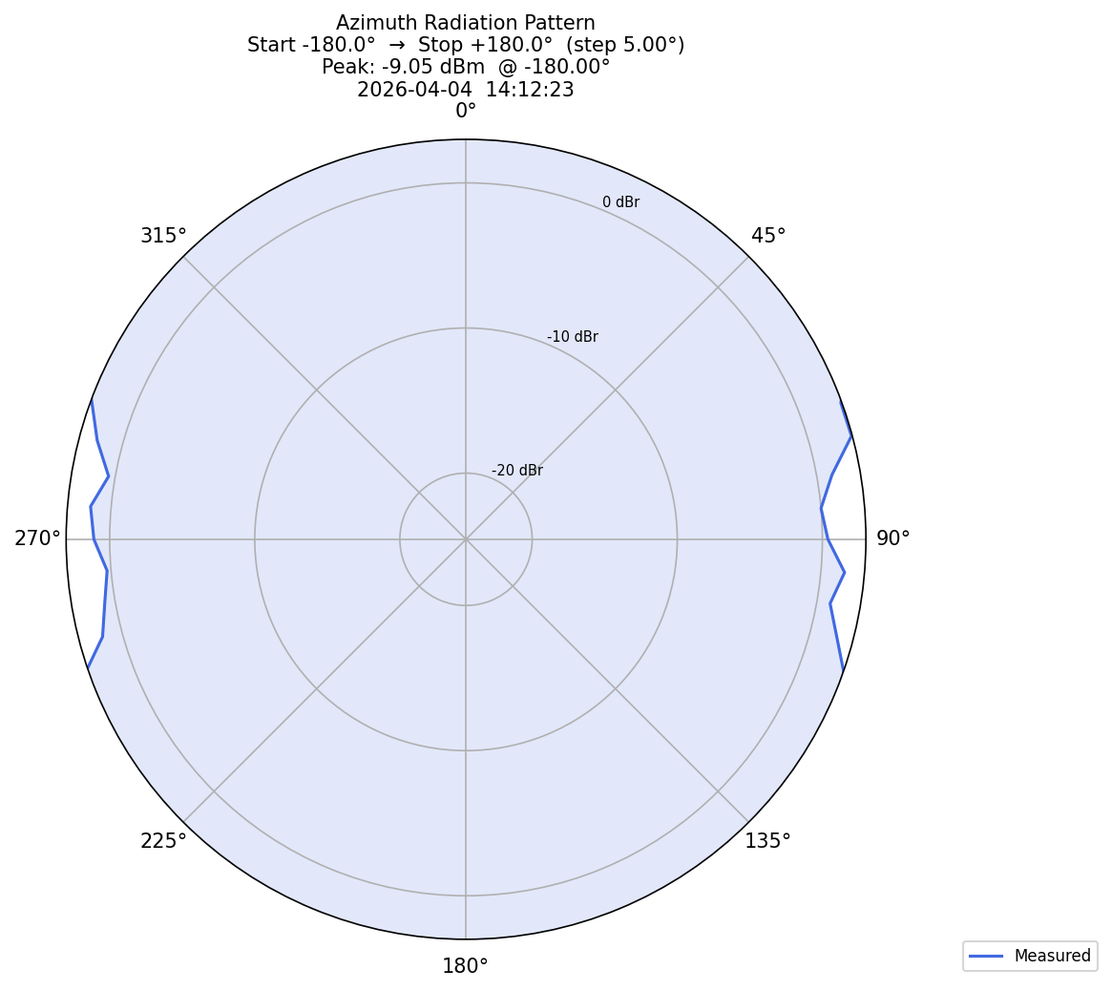
Software/ChamberTesting/pattern_measurements/pattern_20260404_141123.png
