yilmaz-kaan/OpenPhasedArray/Software/ChamberTesting/pattern_measurements/pattern_20260406_172345.png

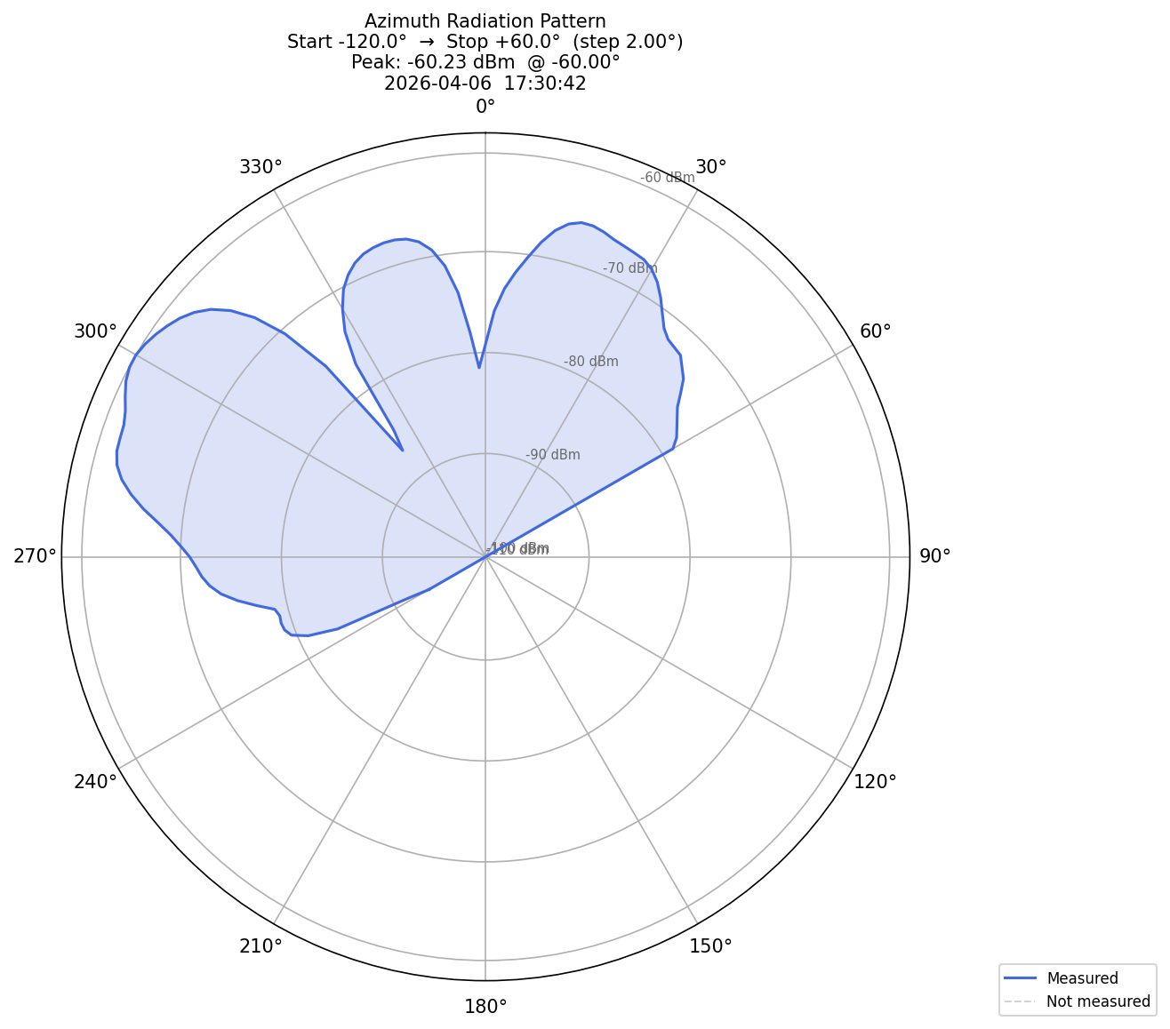
Software/ChamberTesting/pattern_measurements/pattern_20260406_172345.png
