yilmaz-kaan/OpenPhasedArray/Software/ChamberTesting/pattern_measurements/pattern_20260407_132953_P32-60-24-52.png

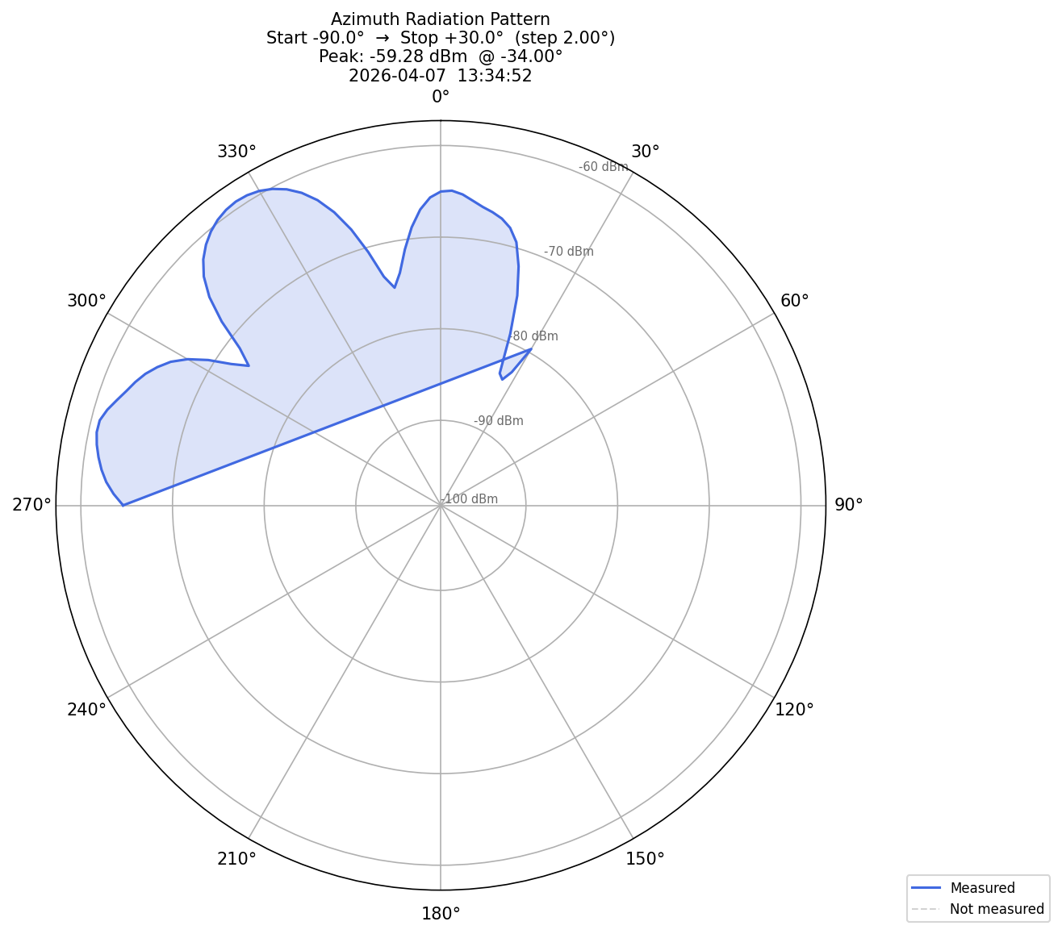
Software/ChamberTesting/pattern_measurements/pattern_20260407_132953_P32-60-24-52.png
