yilmaz-kaan/OpenPhasedArray/Software/ChamberTesting/pattern_measurements/pattern_20260409_155944.png

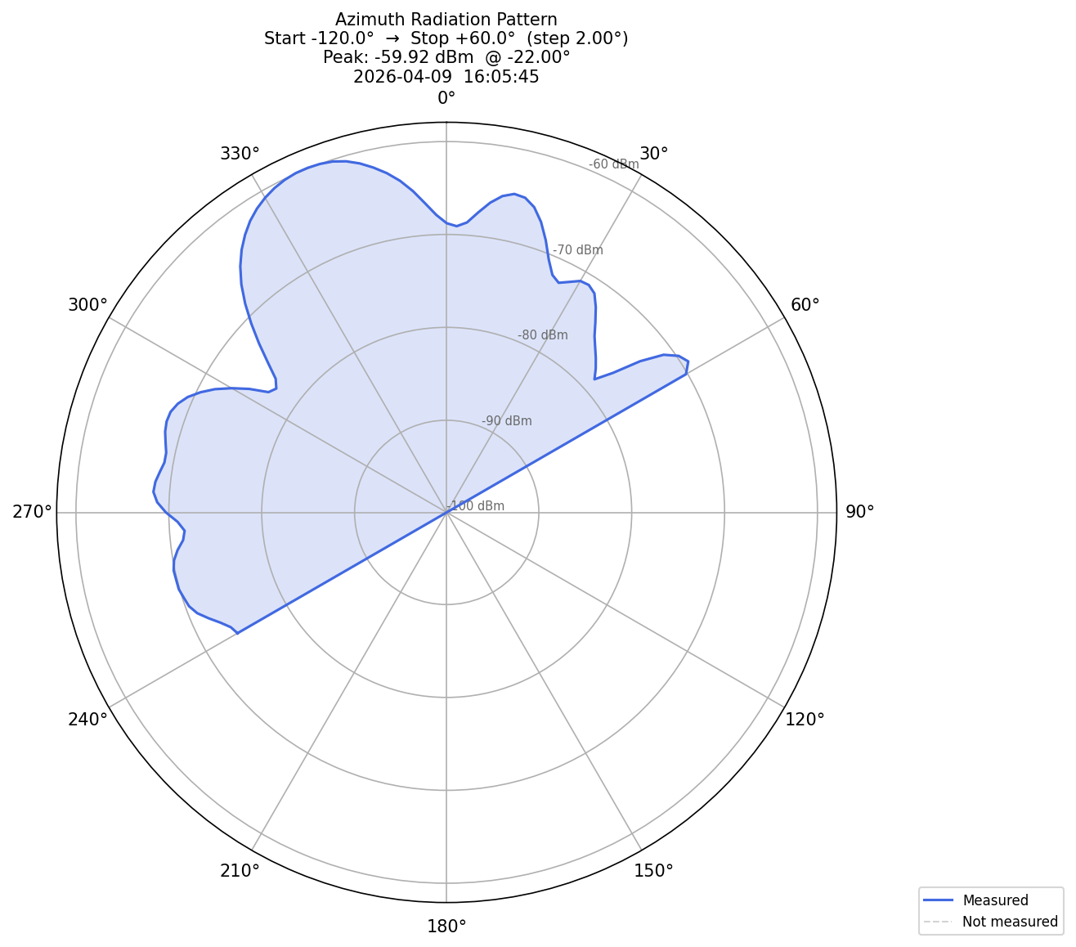
Software/ChamberTesting/pattern_measurements/pattern_20260409_155944.png
