yilmaz-kaan/OpenPhasedArray/Software/ChamberTesting/pattern_measurements/pattern_table0.png

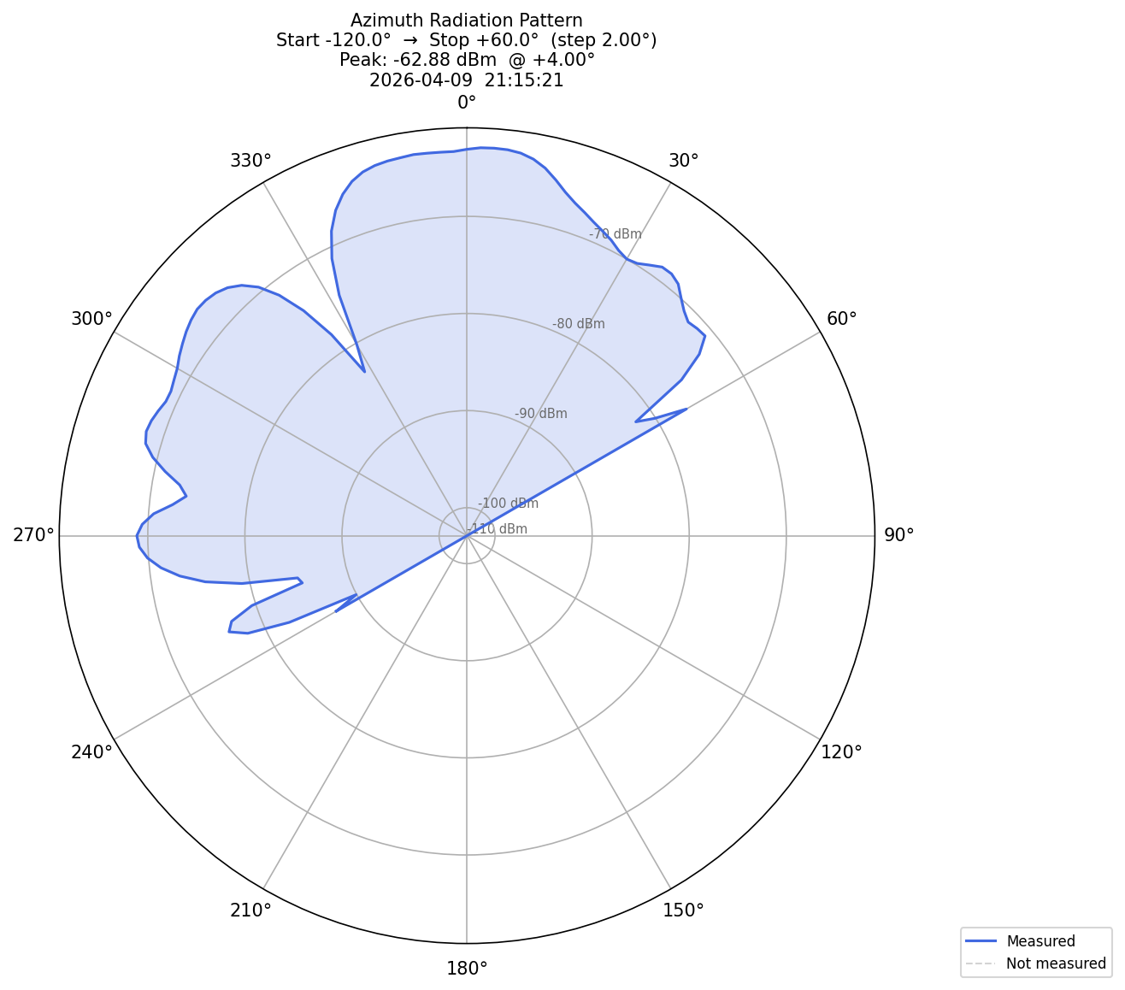
Software/ChamberTesting/pattern_measurements/pattern_table0.png
