yilmaz-kaan/OpenPhasedArray/Software/ChamberTesting/pattern_measurements/pattern_table+15.png

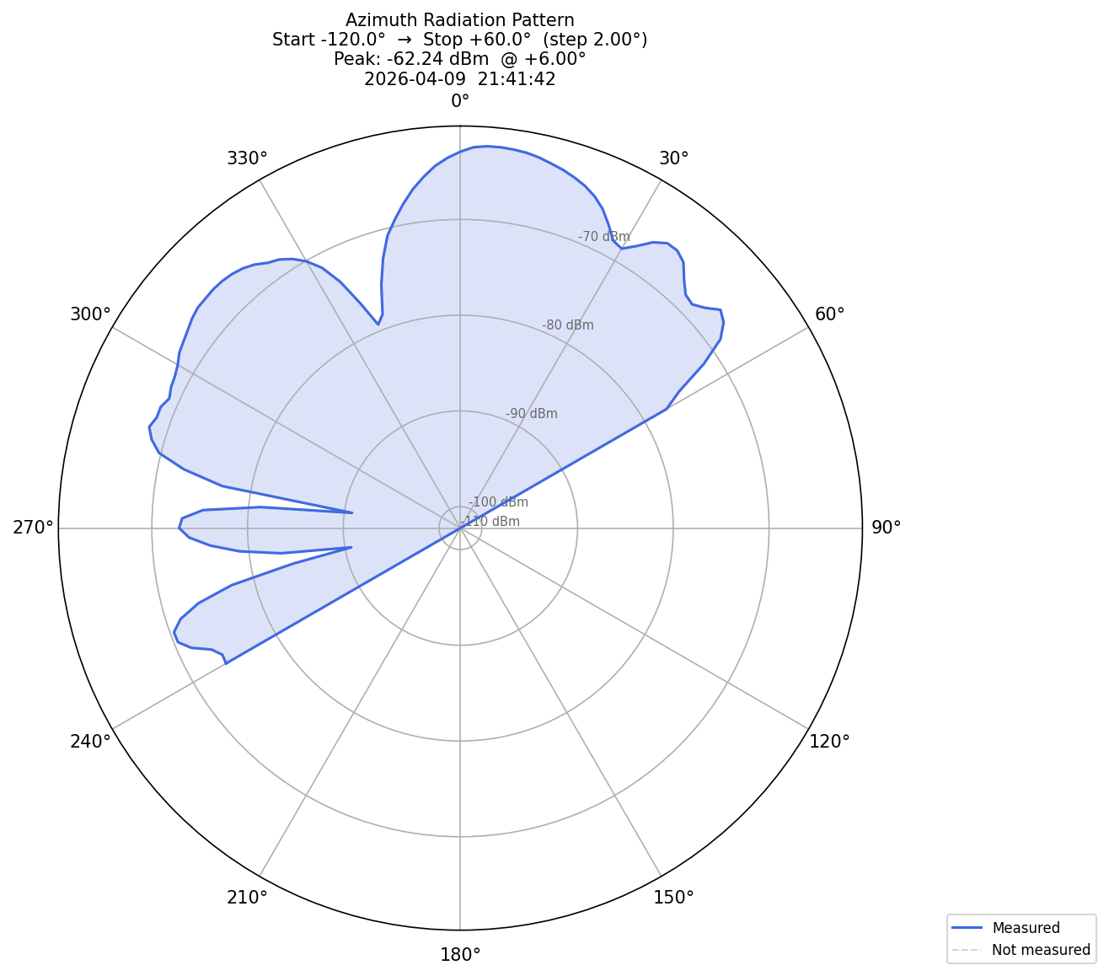
Software/ChamberTesting/pattern_measurements/pattern_table+15.png
