yilmaz-kaan/OpenPhasedArray/Software/ChamberTesting/pattern_measurements/pattern_table-45.png

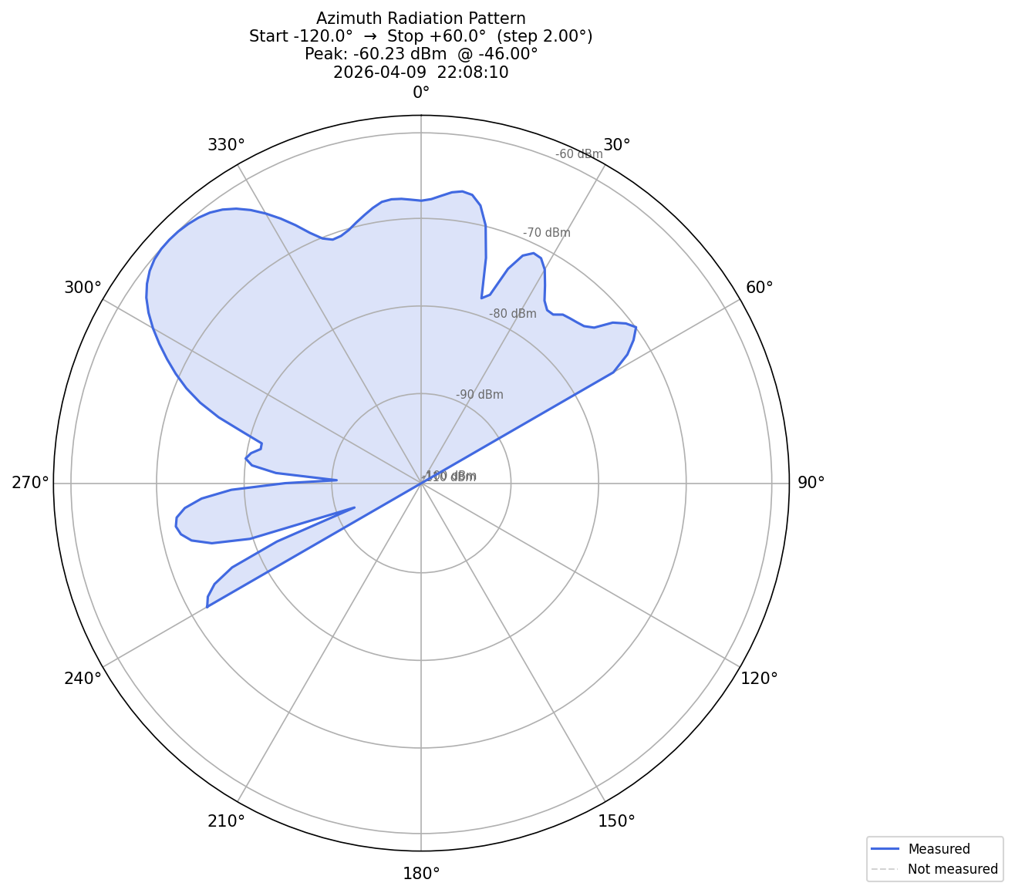
Software/ChamberTesting/pattern_measurements/pattern_table-45.png
