yilmaz-kaan/OpenPhasedArray/Software/ChamberTesting/pattern_measurements/pattern_table-75.png

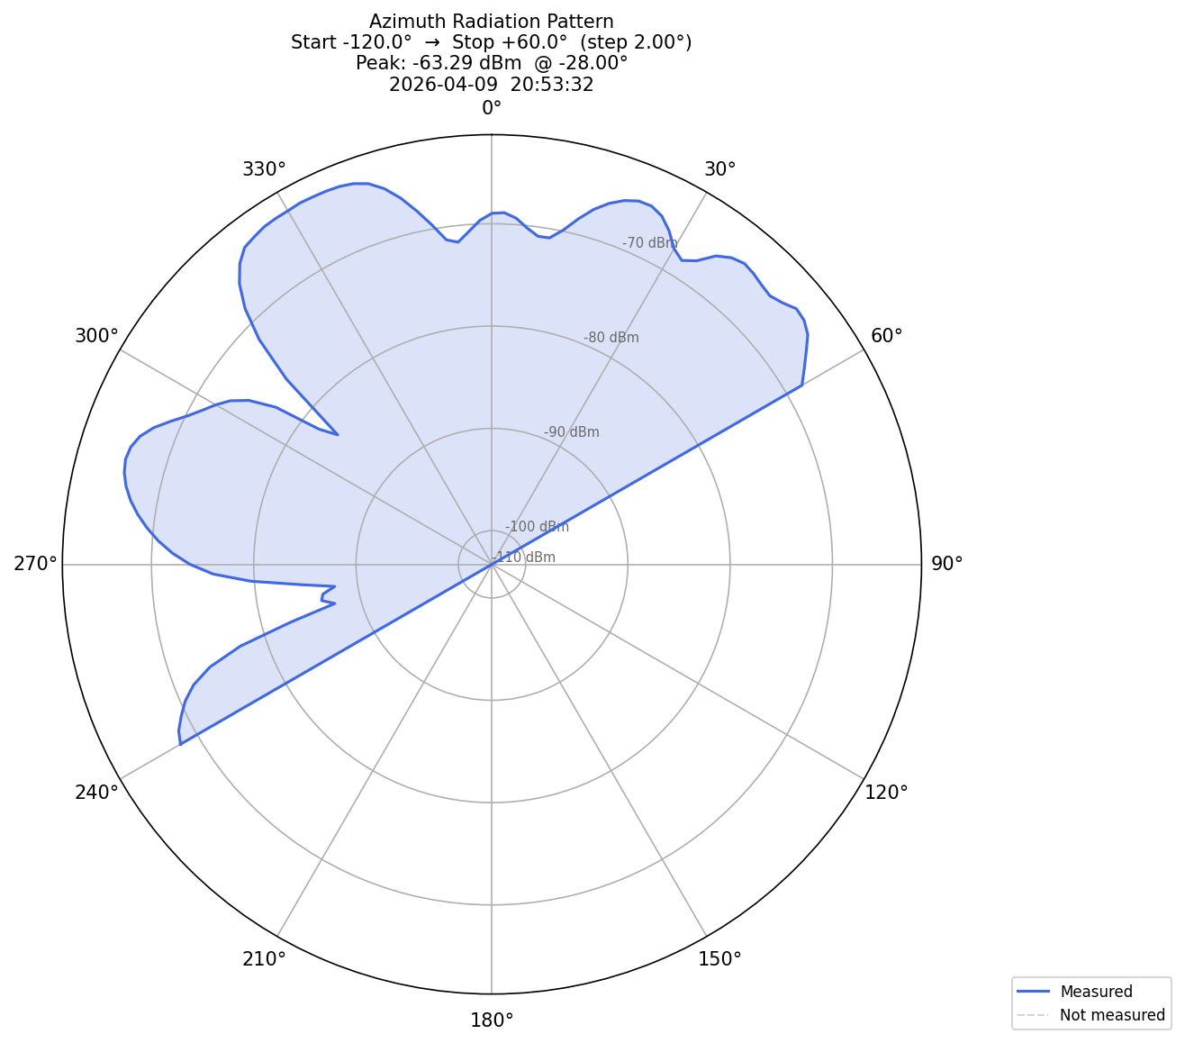
Software/ChamberTesting/pattern_measurements/pattern_table-75.png
